dodo-12-37/TrackSense/Composants/Acceleromètre/QMC5883L - Boussole/HMC5883L(Or QMC5883L) Electronic.pdf

# HMC5883L(Or QMC5883L) Electronic Compass

In ourProfessional Kit, there exist two kinds of Compass module. One kind uses HMC5883L module, the other uses QMC5883L module. You will get one of them when you get the Professional Kit. They don't have too much difference. HMC5883Lis made by Honeywell. but because the production is about to be stopped, so we use a similar compass module-QMC5883Linstead. QMC5883Lis made by a Chinese company, they get the production authorization of HMC5883L from Honeywell, and rename it QMC5883L. So QMC5883Land HMC5883Lbasically are the same, they shares the same hardware design. Just their register is a bit different. We only need to change the software a bit.

When you got the Professional Kit, please check which compass module you get based on the following picture. The HMC5883Lhas a label "L883"on it, while QMC5883Lcomes with "5883"

HMC5883LElectronic Compass | QMC5883LElectronic Compass
HMC5883LElectronic Compass | QMC5883LElectronic Compass

# HMC5883L Electronic Compass

## Introduction

3-Axis Compass module, I2C based Honeywell HMC5883 digital compass. This ASIC is equipped with high resolution HMC118X magneto-resistive sensors and a 12-bitADC. It provides compass heading accuracy up to 1° to 2°. Signal conditioning like amplification, automatic degaussing strap drivers and offset cancellation are inbuilt. This module also includes a MIC5205-2.5 voltage regulator for power supply requirement. Hence user can connect any 3.3V to 6V DC power supply.

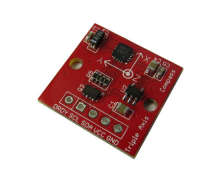
[picture p6: figure]

## Features

- I2C interface
- Compatible with 3.3V-5.0V voltage level
- Max 116Hz output rate
- High heading accuracy

## Usage

Below is a registermap that might help you understand what you can get from this module. There are totally 13 registers provided by HMC5883L. Out of three registers - Configuration registerA, Configuration RegisterB and Mode Register decide the working mode of the device. The remaining registers are read only data output registers, status register and identification registers.

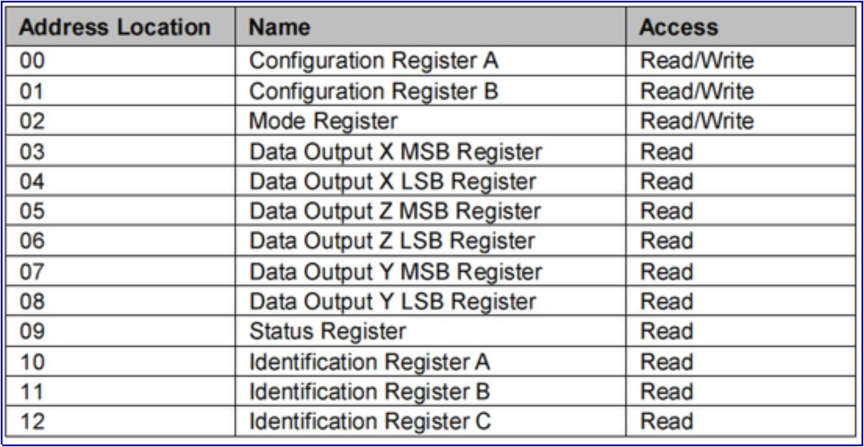
[picture p7: figure]

This demo is going to show you how to read raw data, how to calibrate the data with your local magnetic declination angle and how to get heading angle.
First off, before any action you are going to take, you need to prepare a parameter you are going to use in your demo. That's your local magnetic declination.
You can find it out in degree via the magnetic declination webpage. For example, mine is -2°37’, which is -2.617 degree.
Then transfer it from degree to radians, and there you get the "declinationAngle". For example, in my case, declinationAngle = -2.617 / （2*π）= -0.0456752665 rad. Three significant figures are enough. So I would shorten it into -0.0456 rad. And this is the parameter you are going to replace the value of "declinationAngle"in the domo code with.
Now let's start to run your compass.
1. Connect the HMC5883LElectronic Compass to Arduino via the I2C port.
2. Download the library file: HMC5883L Compass library. Unzip it into the libraries file of Arduino IDE by the path: ..\arduino-1.0.1\libraries.
3. Open the demo by the path:File -> Example ->Digital Compass ->HMC5883L_Example.
4. Replace the value of variable "declinitionAngle"with the one you've figured out already.
5. Upload the Code.
6. Check the output result by opening the serial monitor.

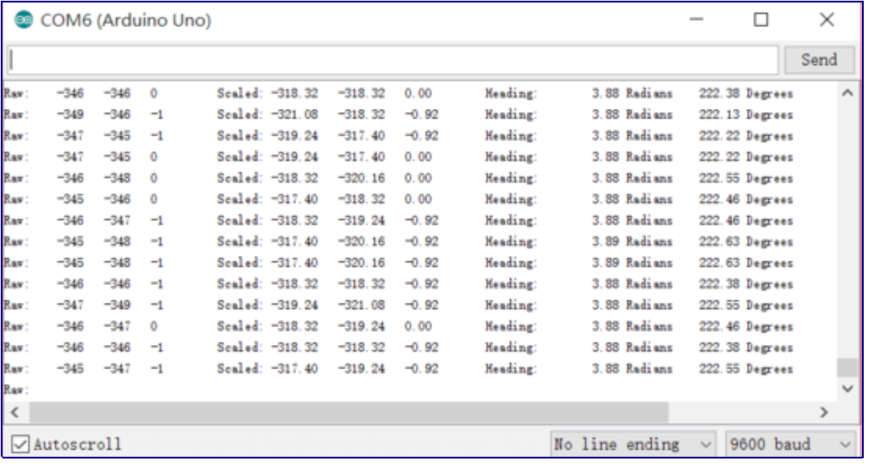
[picture p8: figure]

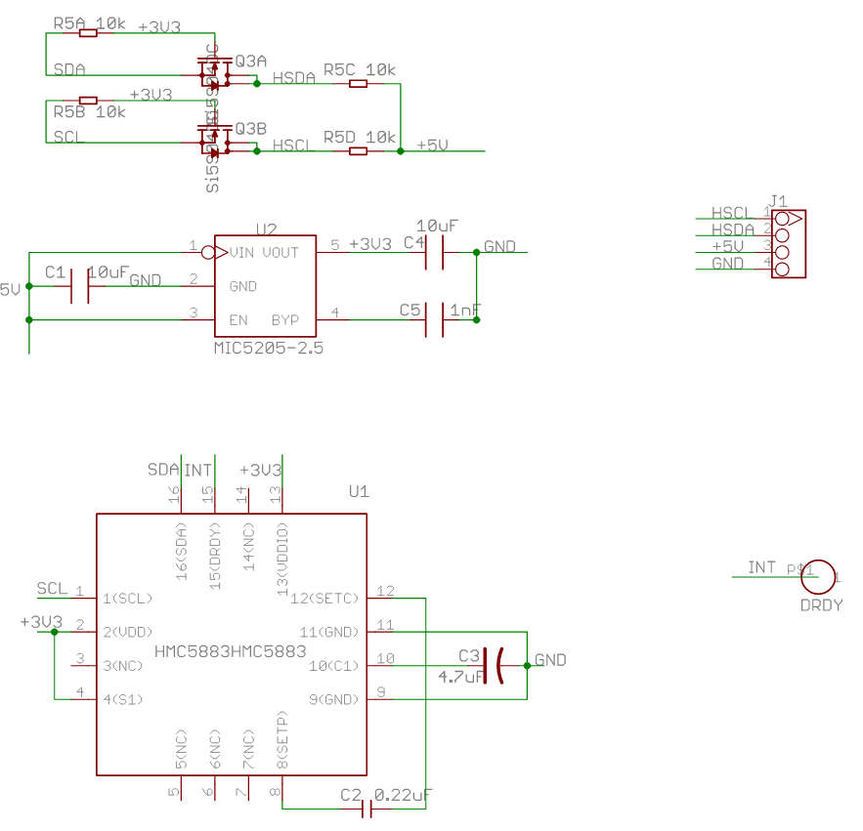
[picture p9: figure]

# QMC5883L Electronic Compass

## Introduction

3-Axis Compass module, I2C based QMC5883 digital compass. This ASIC is equipped with high resolution magneto-resistive sensors and a 16-bit ADC. It provides compass heading accuracy up to 1° to 2°. Signal conditioning like amplification, automatic degaussing strap drivers and offset cancellation are inbuilt. This module also includes a MIC5205-2.5 voltage regulator forpower supply requirement. Hence user can connect any 3.3V to 6V DC power supply.

Features

- I2C interface
- Compatible with 3.3V-5.0V voltage level
- Max 200Hz output rate
- High heading accuracy

## Usage

Below is a registermap that might help you understand what you can get from this module. There are totally 14 registers provided by QMC5883L. Two Control Registers decide the working mode of the device, they come with address "09H"and "0AH". Most of the remaining registers are read only data output registers, status register and identification registers.

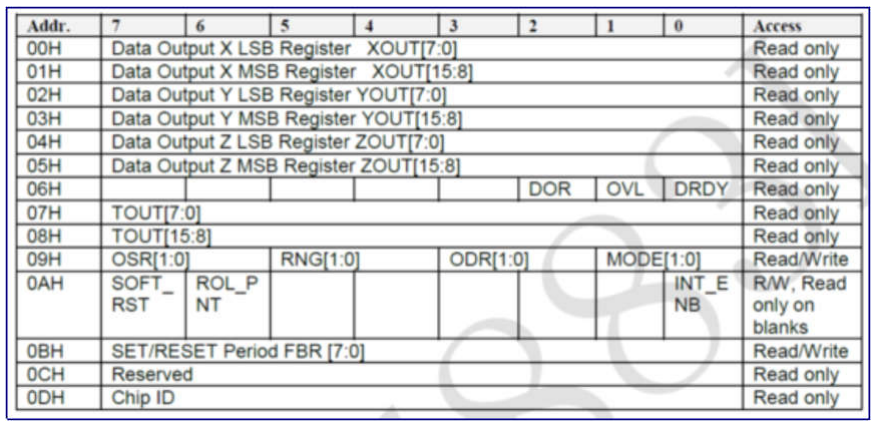
[picture p10: figure]

In this example we will make the module output the heading angle between South and this module.

### 1. Connect the QMC5883LElectronic Compass to Arduino via the I2C port. Make sure the

QMC5883L module is horizontal。
2. Download the library file: QMC5883L Compass library. Unzip it into the libraries file of Arduino IDE by the path: ..\arduino-1.0.1\libraries.
3. Open the demo by the path:File -> Example ->Digital Compass ->QMC5883L_Example.
4. Upload the Code.
5. Check the output result by opening the serial monitor.

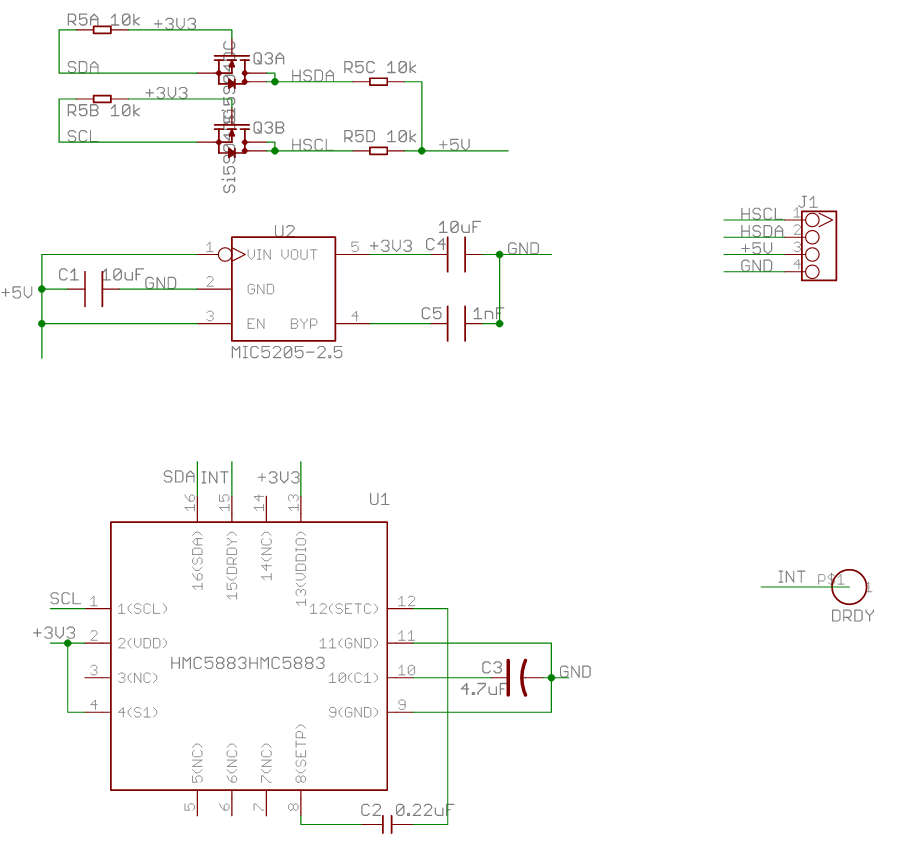
[picture p11: figure]
