dodo-12-37/TrackSense/Composants/Acceleromètre/Dessous Sensor.jpg

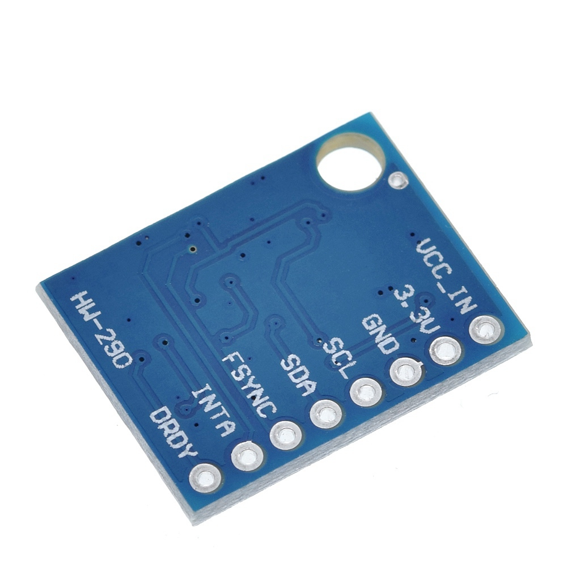
Composants/Acceleromètre/Dessous Sensor.jpg
