dodo-12-37/TrackSense/Composants/Acceleromètre/Dessus Dessous Sensor.jpg

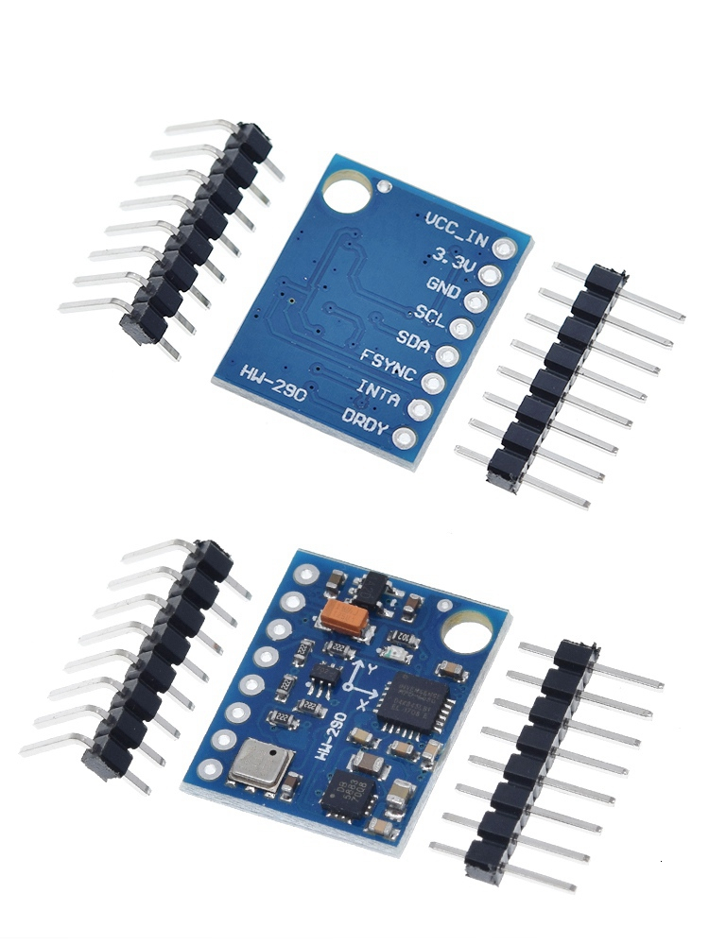
Composants/Acceleromètre/Dessus Dessous Sensor.jpg
