dodo-12-37/TrackSense/Composants/Acceleromètre/Dessus Sensor 2.jpg

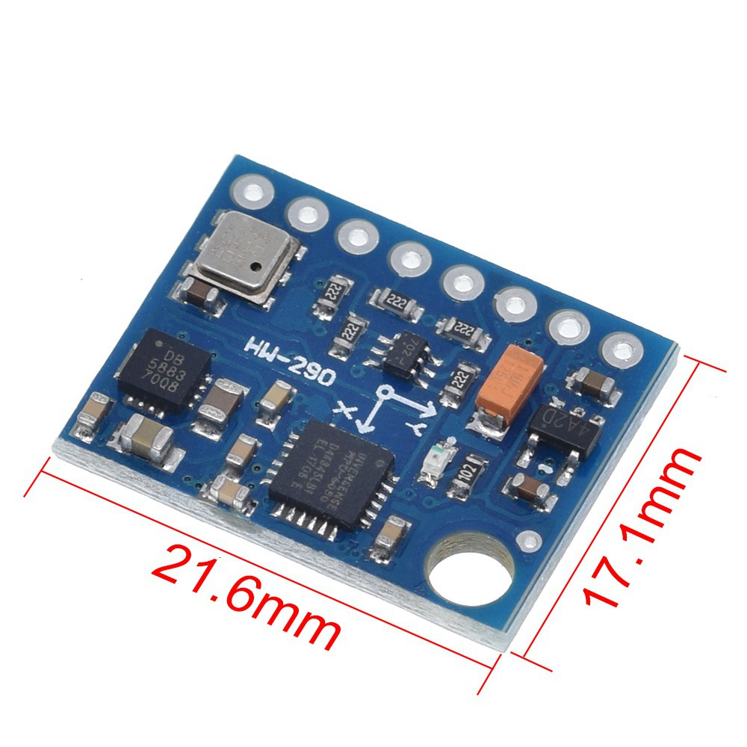
Composants/Acceleromètre/Dessus Sensor 2.jpg
