dodo-12-37/TrackSense/Composants/Acceleromètre/Dessus Sensor.jpg

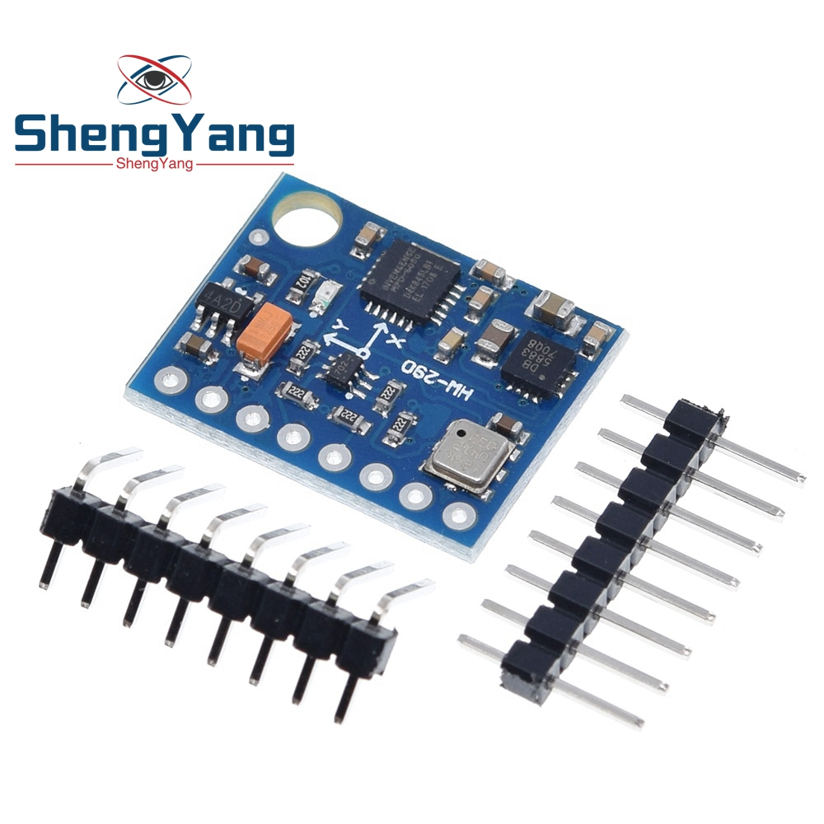
Composants/Acceleromètre/Dessus Sensor.jpg
