dodo-12-37/TrackSense/Composants/Acceleromètre/GY-87-Module-wire-4.jpg

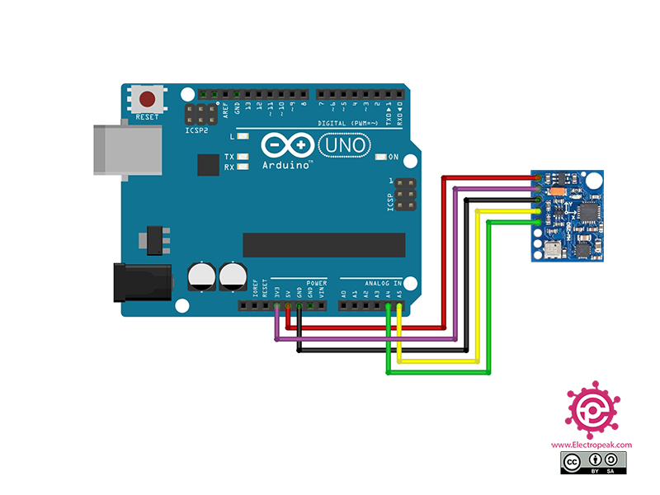
Composants/Acceleromètre/GY-87-Module-wire-4.jpg
