dodo-12-37/TrackSense/Composants/Acceleromètre/GY-87-Pin-2.jpg

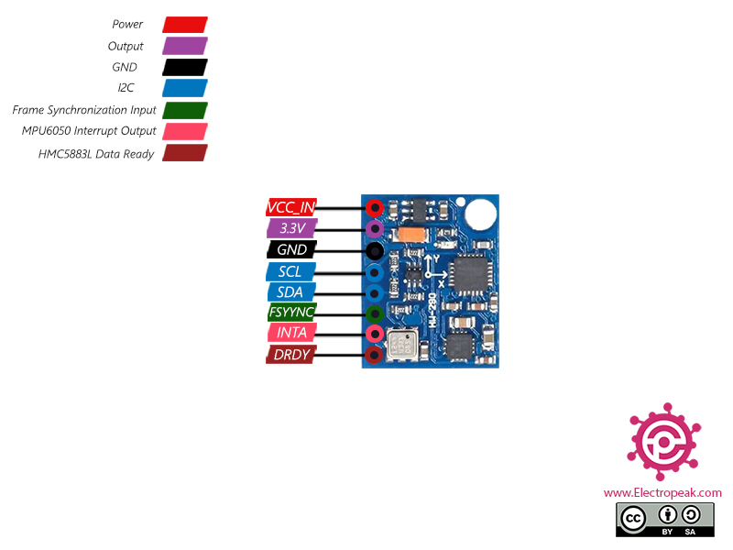
Composants/Acceleromètre/GY-87-Pin-2.jpg
