dodo-12-37/TrackSense/Composants/Acceleromètre/QMC5883L - Boussole/Dessins Boussole/Boussoles2.png

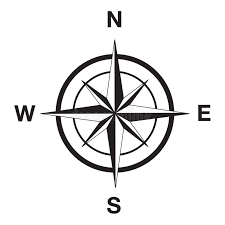
Composants/Acceleromètre/QMC5883L - Boussole/Dessins Boussole/Boussoles2.png
