dodo-12-37/TrackSense/Composants/Boitier/Photos_boitier/Bitoniau 1.png

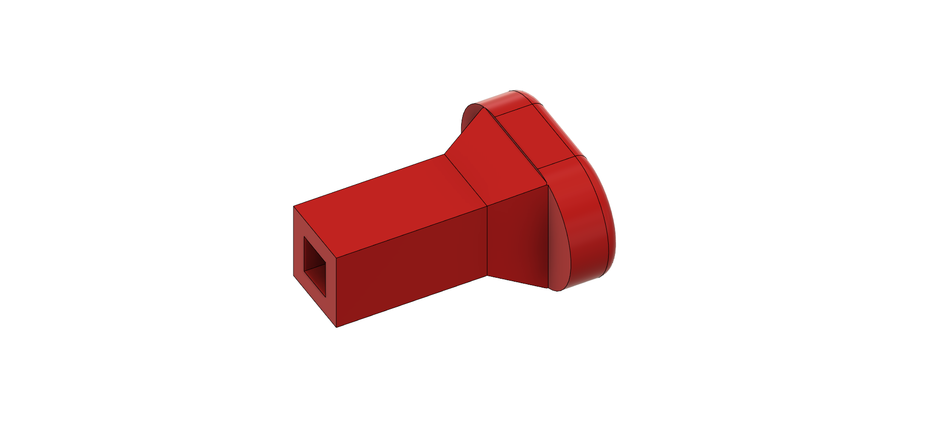
Composants/Boitier/Photos_boitier/Bitoniau 1.png
