dodo-12-37/TrackSense/Composants/Boitier/Photos_boitier/Bitoniau 2.png

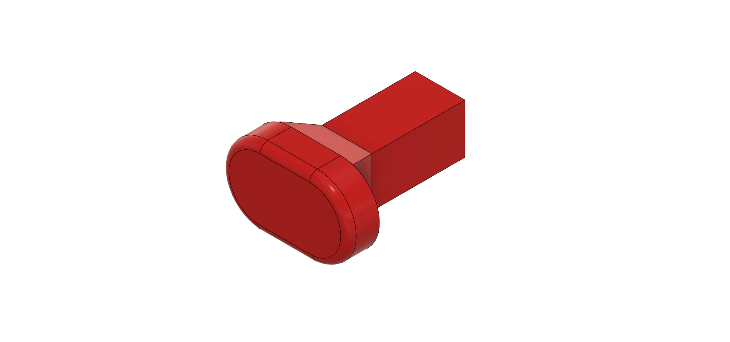
Composants/Boitier/Photos_boitier/Bitoniau 2.png
