dodo-12-37/TrackSense/Composants/Boitier/Photos_boitier/Boitier 0.jpg

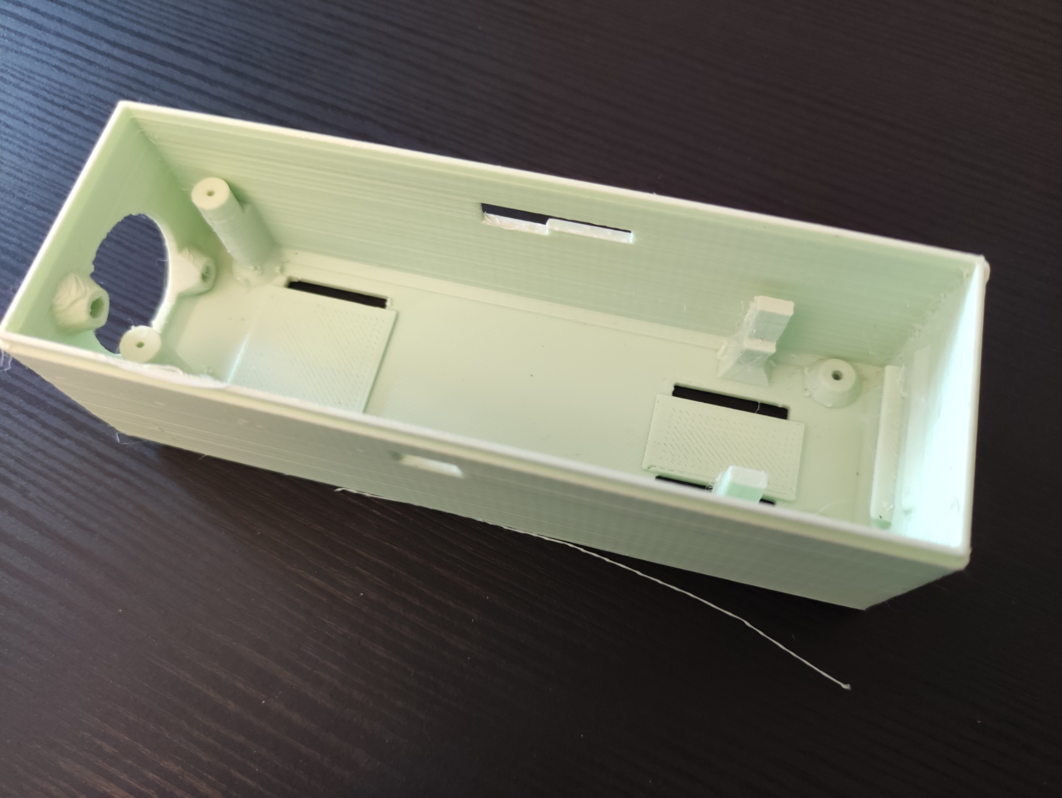
Composants/Boitier/Photos_boitier/Boitier 0.jpg
