dodo-12-37/TrackSense/Composants/Boitier/Photos_boitier/Boitier 3.png

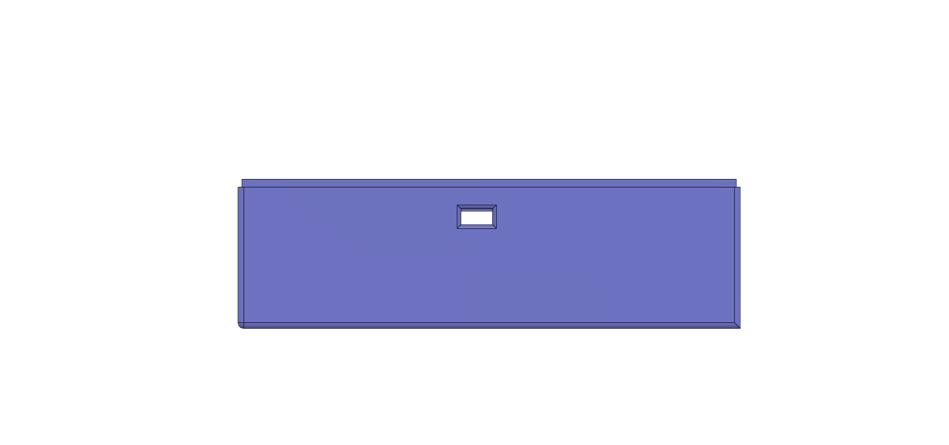
Composants/Boitier/Photos_boitier/Boitier 3.png
