dodo-12-37/TrackSense/Composants/Boitier/Photos_boitier/Boitier 5.png

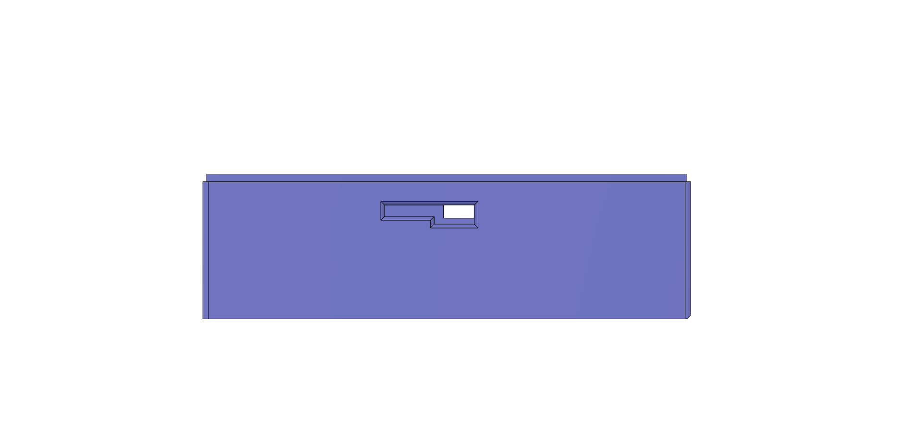
Composants/Boitier/Photos_boitier/Boitier 5.png
