dodo-12-37/TrackSense/Composants/Boitier/Photos_boitier/Couvercle 1.png

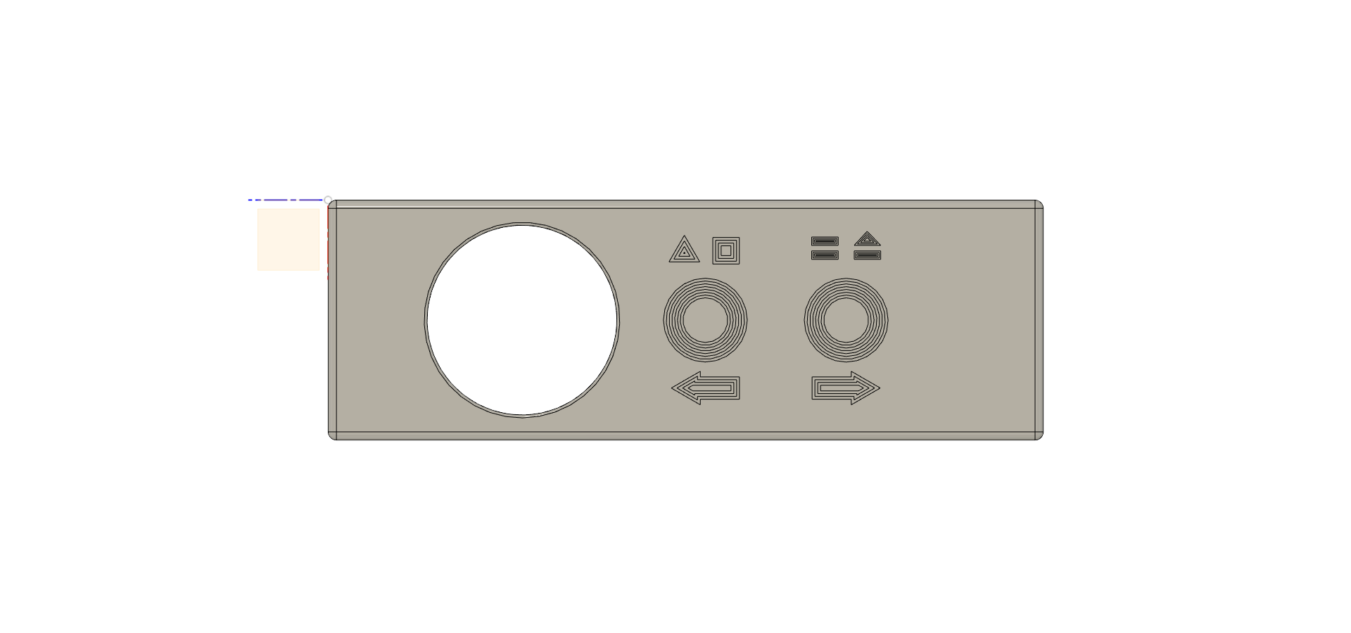
Composants/Boitier/Photos_boitier/Couvercle 1.png
