dodo-12-37/TrackSense/Composants/Boitier/Photos_boitier/Ensemble 1.jpg

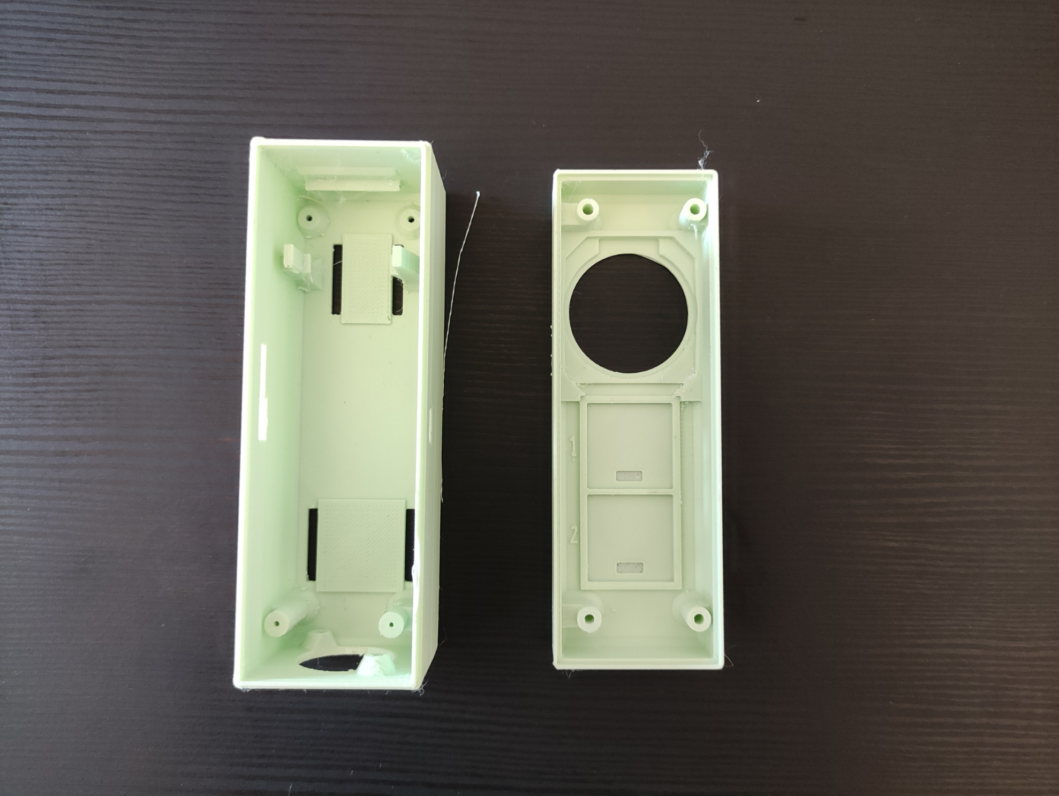
Composants/Boitier/Photos_boitier/Ensemble 1.jpg
