dodo-12-37/TrackSense/Composants/Boitier/Photos_boitier/Ensemble 2.png

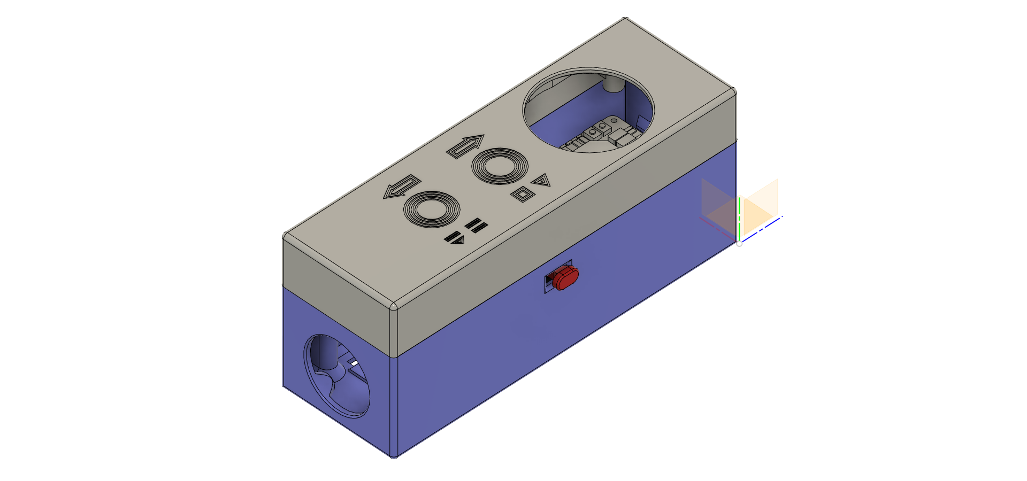
Composants/Boitier/Photos_boitier/Ensemble 2.png
