dodo-12-37/TrackSense/Composants/Boutons tactiles/Dessous Sensor.jpg

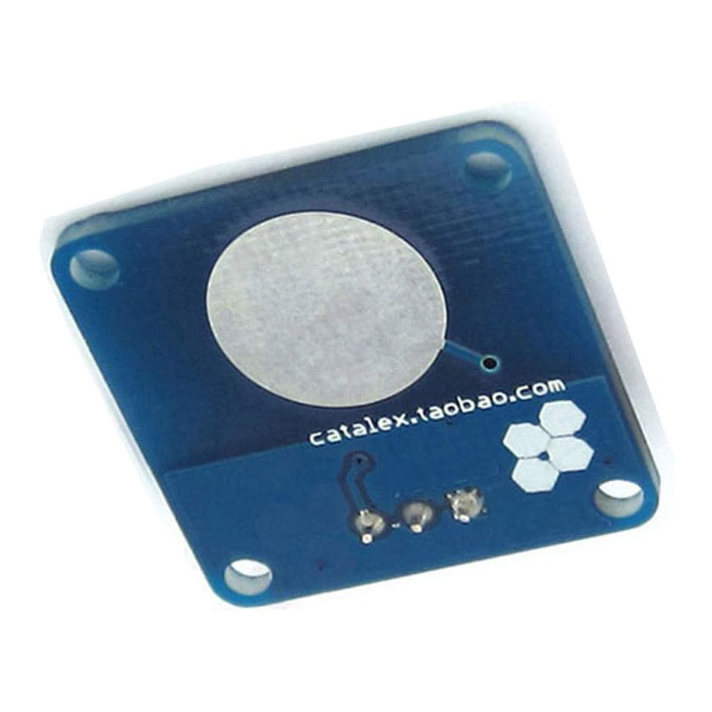
Composants/Boutons tactiles/Dessous Sensor.jpg
