dodo-12-37/TrackSense/Composants/Boutons tactiles/Dessus Sensor.jpg

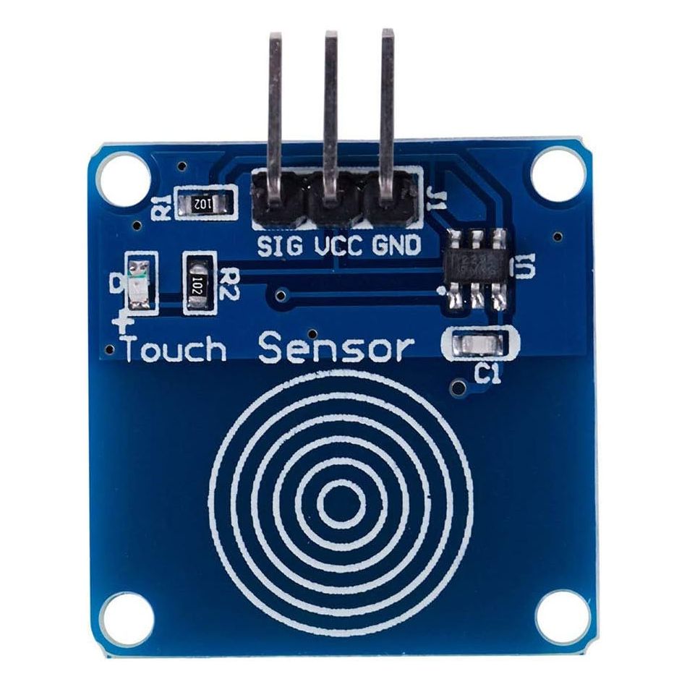
Composants/Boutons tactiles/Dessus Sensor.jpg
