dodo-12-37/TrackSense/Composants/Boutons tactiles/Digital-Sensor-TTP223B-Module-Capacitive2.webp

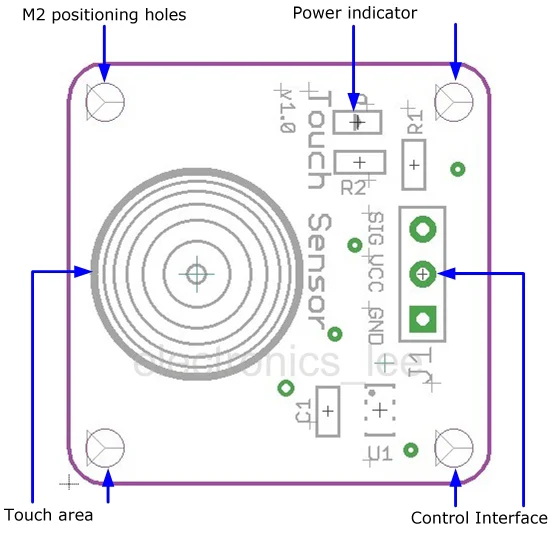
Composants/Boutons tactiles/Digital-Sensor-TTP223B-Module-Capacitive2.webp
