dodo-12-37/TrackSense/Composants/Boutons tactiles/Dimensions 2.JPG

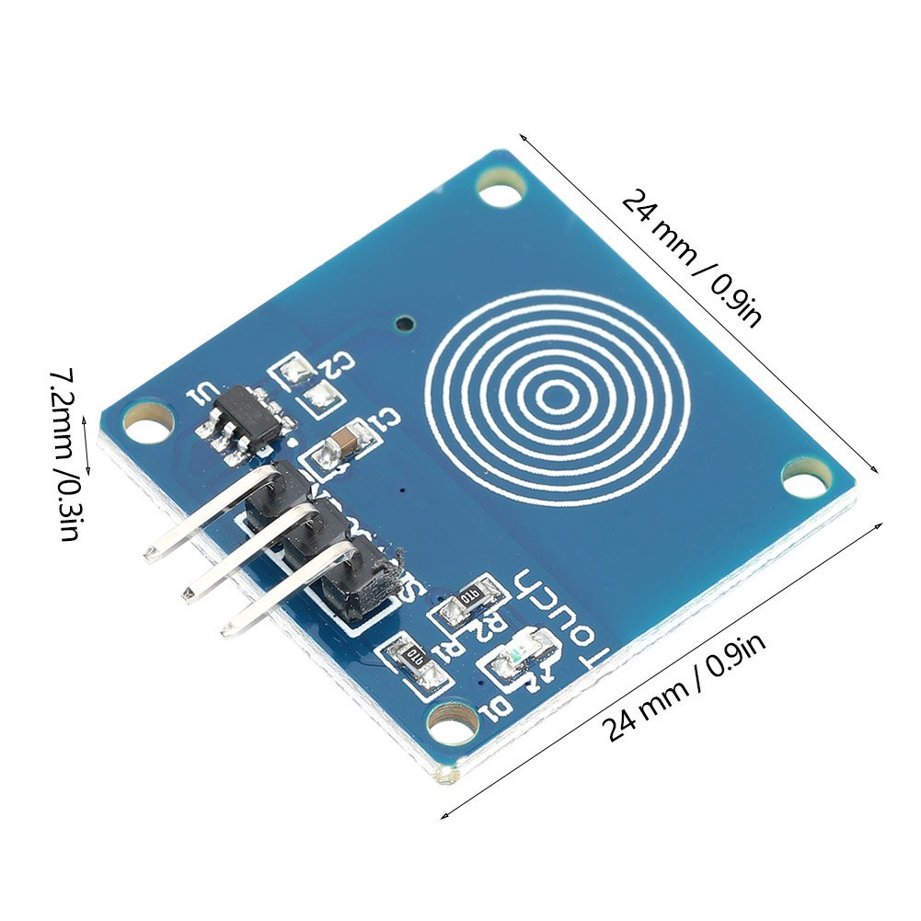
Composants/Boutons tactiles/Dimensions 2.JPG
