dodo-12-37/TrackSense/Composants/Boutons tactiles/Dimensions.JPG

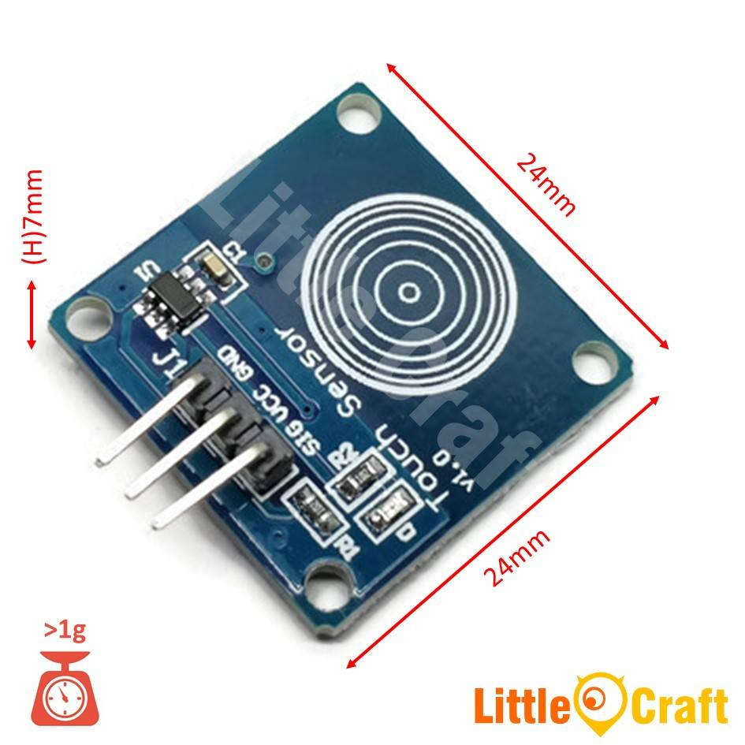
Composants/Boutons tactiles/Dimensions.JPG
