dodo-12-37/TrackSense/Composants/Boutons tactiles/Exemple Connexion Arduino 2.jpg

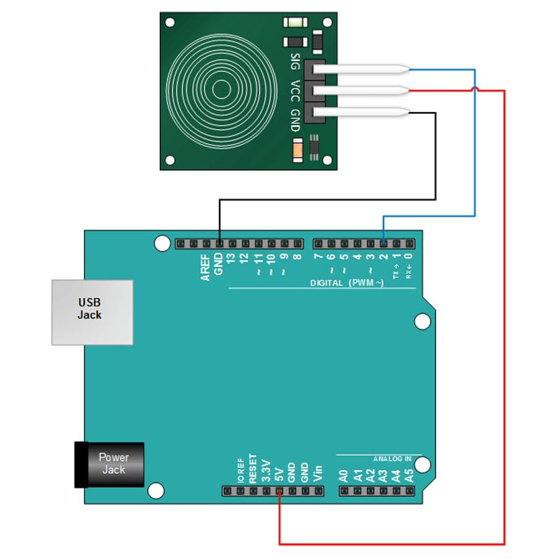
Composants/Boutons tactiles/Exemple Connexion Arduino 2.jpg
