dodo-12-37/TrackSense/Composants/Boutons tactiles/Exemple Connexion Arduino.jpg

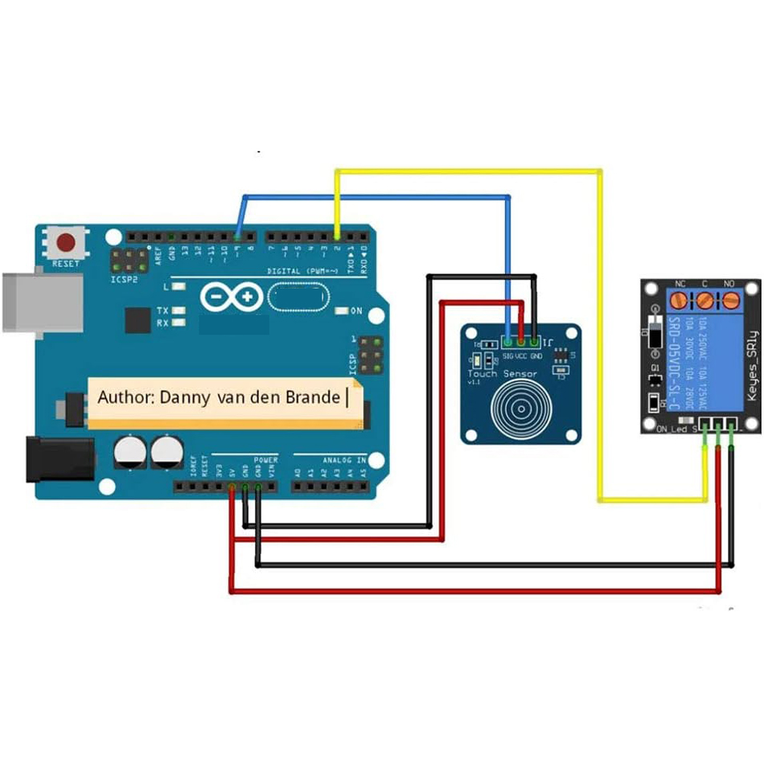
Composants/Boutons tactiles/Exemple Connexion Arduino.jpg
