dodo-12-37/TrackSense/Composants/Boutons tactiles/Exemple Connexion.jpg

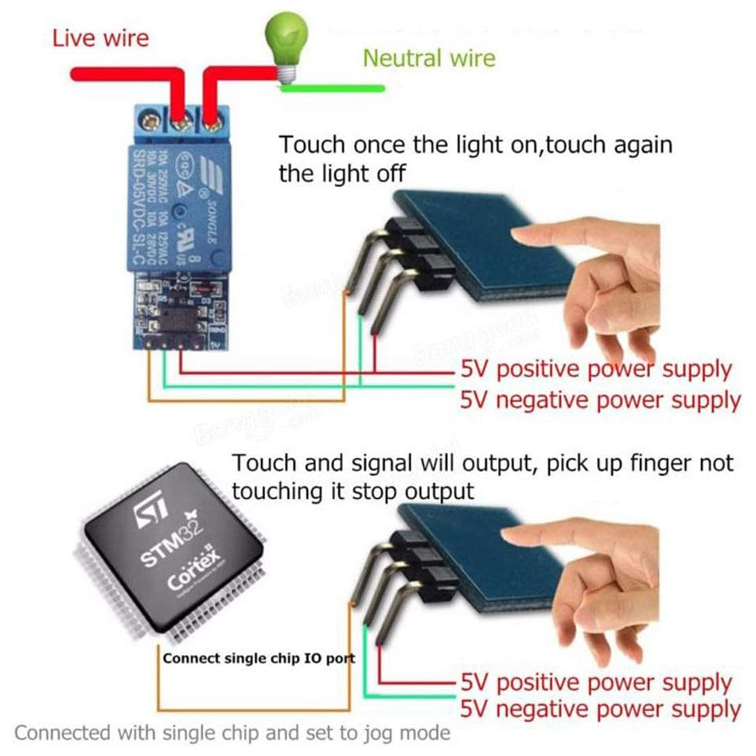
Composants/Boutons tactiles/Exemple Connexion.jpg
