dodo-12-37/TrackSense/Composants/Buzzer/Dessus & Dessous Sensor 2.jpg

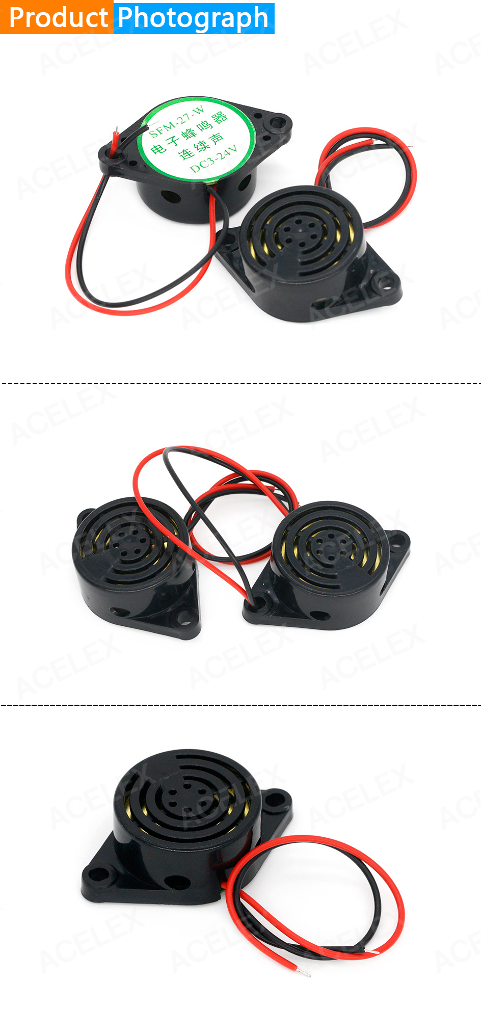
Composants/Buzzer/Dessus & Dessous Sensor 2.jpg
