dodo-12-37/TrackSense/Composants/Buzzer/Dessus & Dessous Sensor.jpg

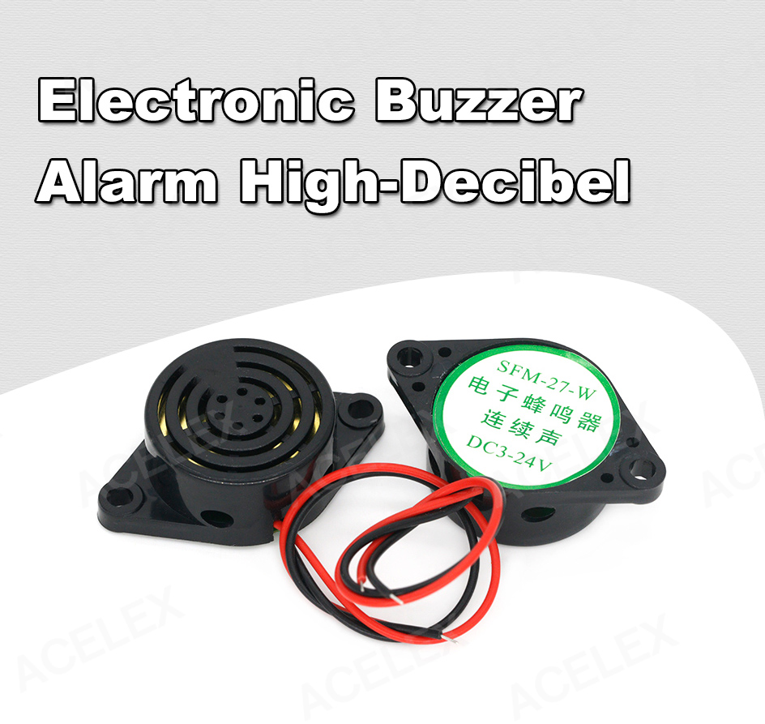
Composants/Buzzer/Dessus & Dessous Sensor.jpg
