dodo-12-37/TrackSense/Composants/Buzzer/Dimension_SFM-20B.jpg

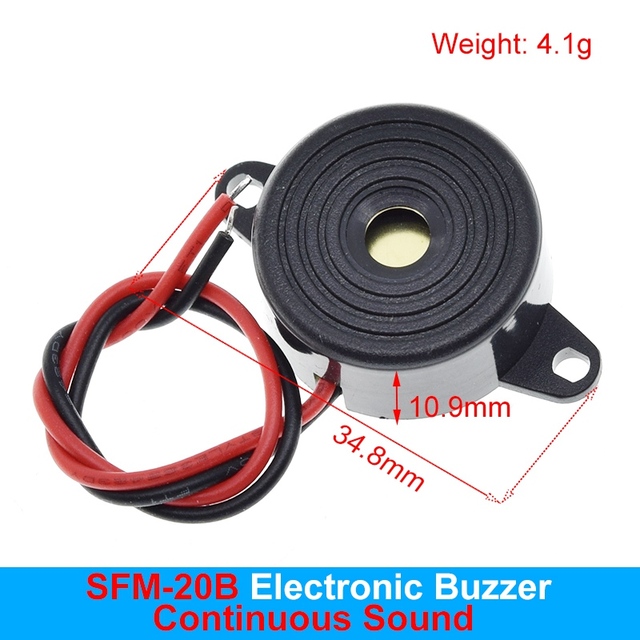
Composants/Buzzer/Dimension_SFM-20B.jpg
