dodo-12-37/TrackSense/Composants/Buzzer/Dimensions_Schéma_SFM-20B.jpg

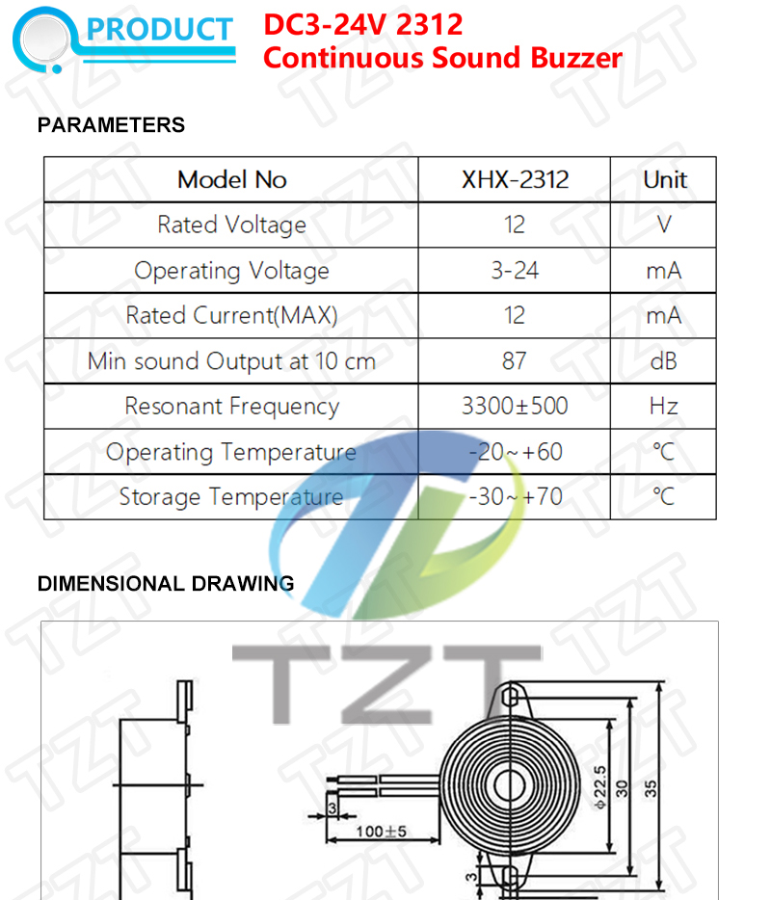
Composants/Buzzer/Dimensions_Schéma_SFM-20B.jpg
