dodo-12-37/TrackSense/Composants/Buzzer/Dimensions_SchémaComplet_SFM-20B.jpg

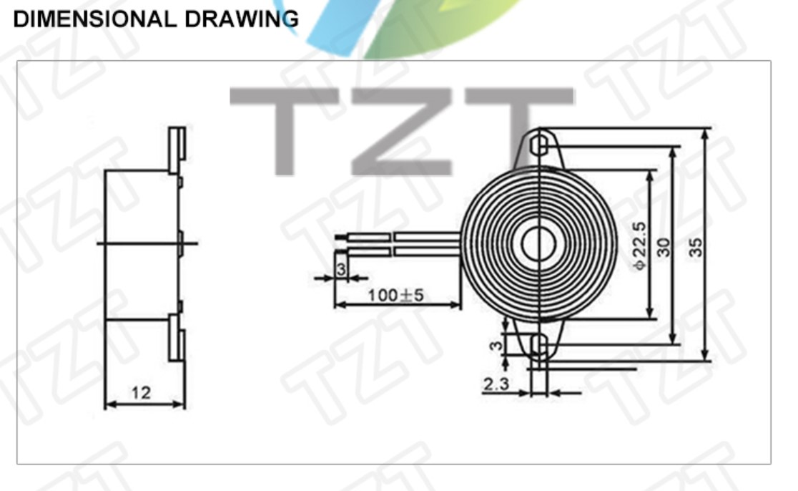
Composants/Buzzer/Dimensions_SchémaComplet_SFM-20B.jpg
