dodo-12-37/TrackSense/Composants/Buzzer/SFM-27/Dimensions_SFM-27_ContinuousSound.jpg

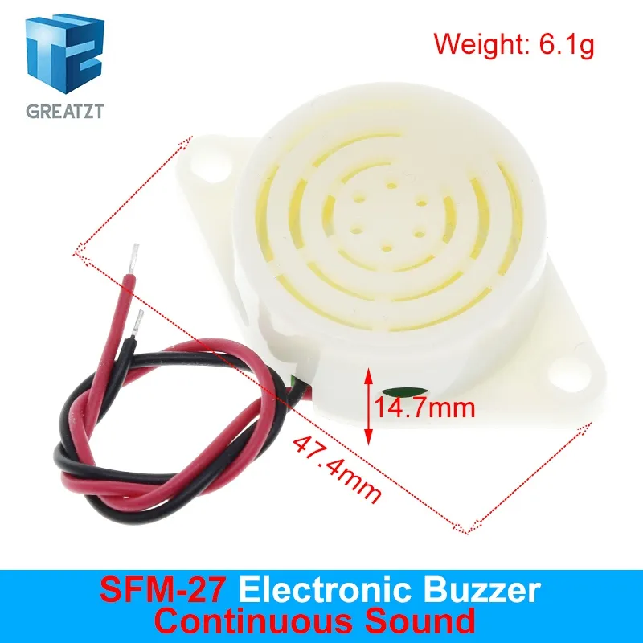
Composants/Buzzer/SFM-27/Dimensions_SFM-27_ContinuousSound.jpg
