dodo-12-37/TrackSense/Composants/Buzzer/SFM-27/Paramètres du Produit SFM-27.jpg

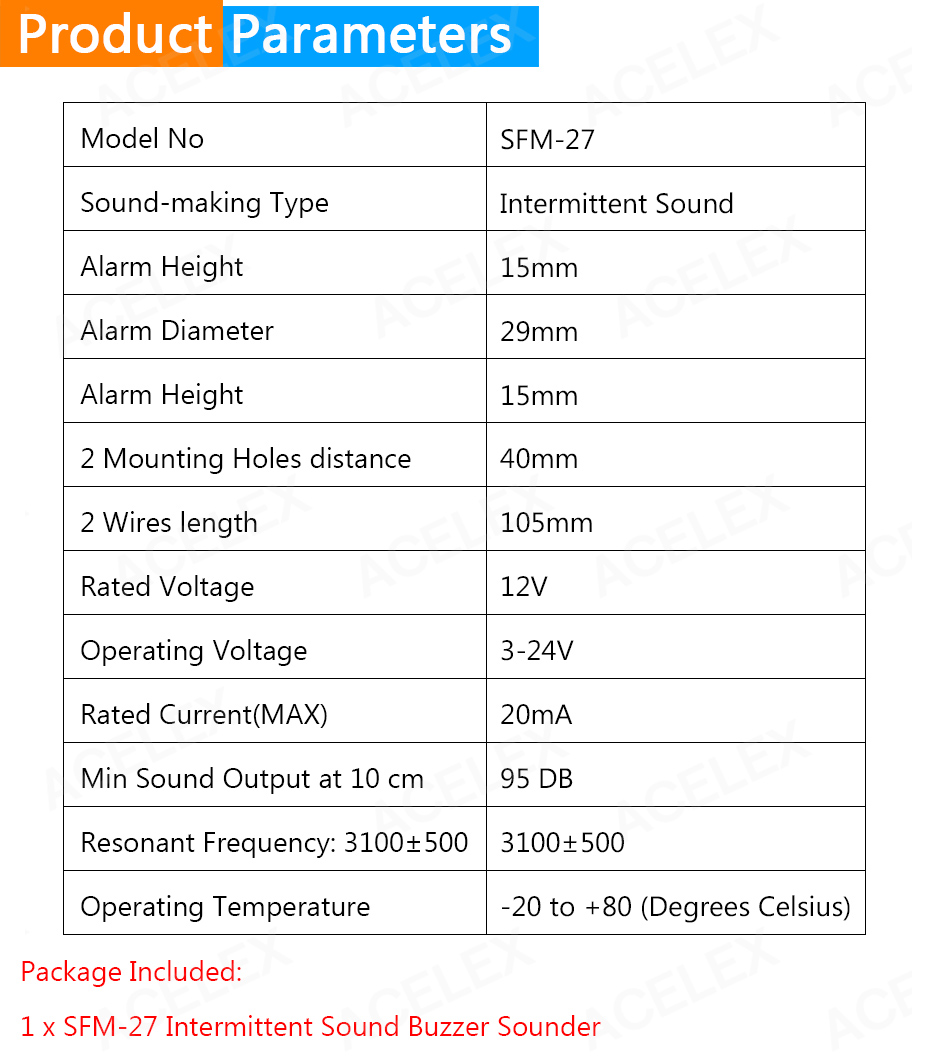
Composants/Buzzer/SFM-27/Paramètres du Produit SFM-27.jpg
