dodo-12-37/TrackSense/Composants/Buzzer/Speaker Alarme SFM-20B XHX-2312 (Pt pas celui acheté).jpg

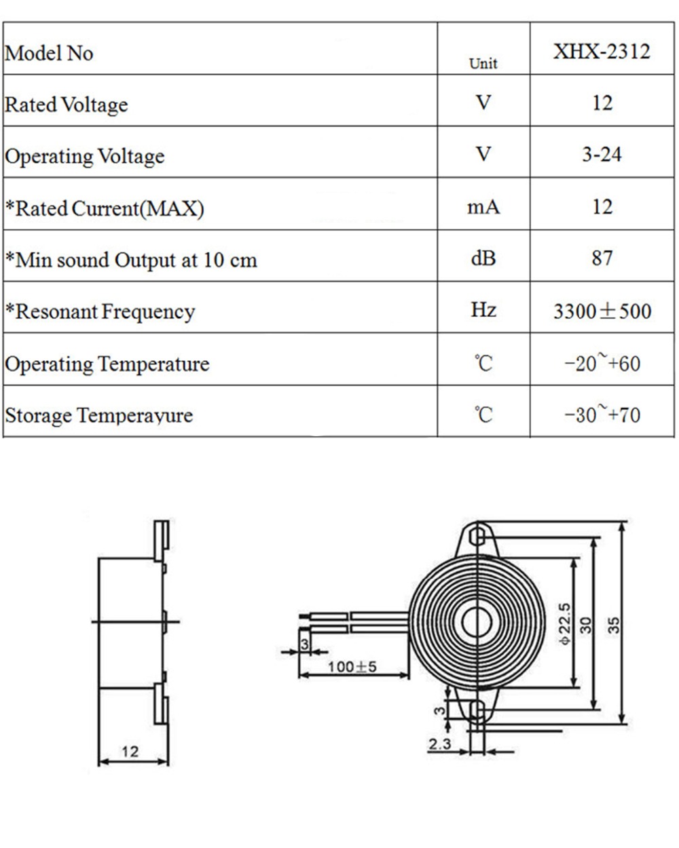
Composants/Buzzer/Speaker Alarme SFM-20B XHX-2312 (Pt pas celui acheté).jpg
