dodo-12-37/TrackSense/Composants/Lilygo/Circuit électrique partielle LILYGO.png

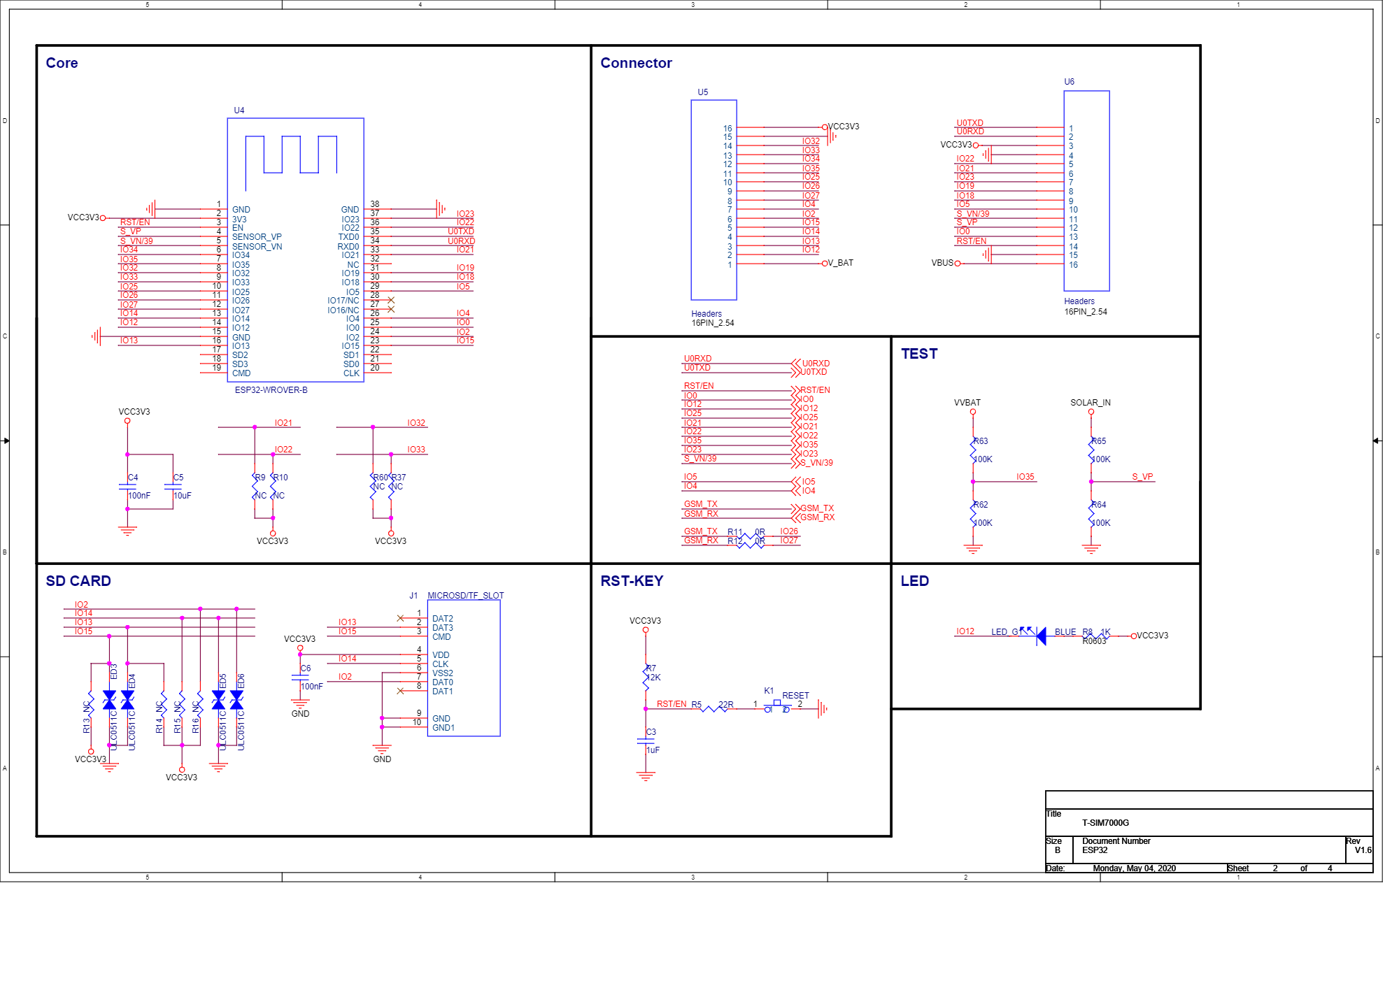
Composants/Lilygo/Circuit électrique partielle LILYGO.png
