dodo-12-37/TrackSense/Composants/Lilygo/Description Aliexpress.png

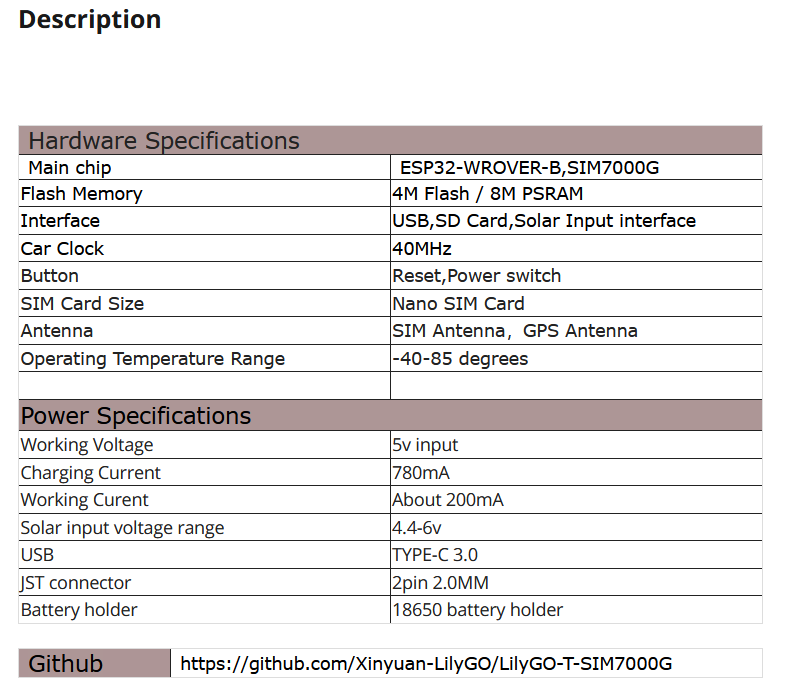
Composants/Lilygo/Description Aliexpress.png
