dodo-12-37/TrackSense/Composants/Lilygo/Dimension de la Plaquette V1.0.png

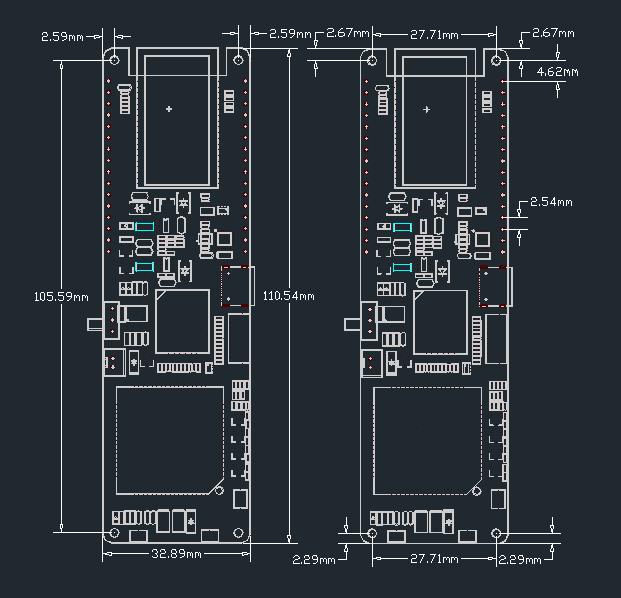
Composants/Lilygo/Dimension de la Plaquette V1.0.png
