dodo-12-37/TrackSense/Composants/Lilygo/Dimension de la Plaquette V1.1.png

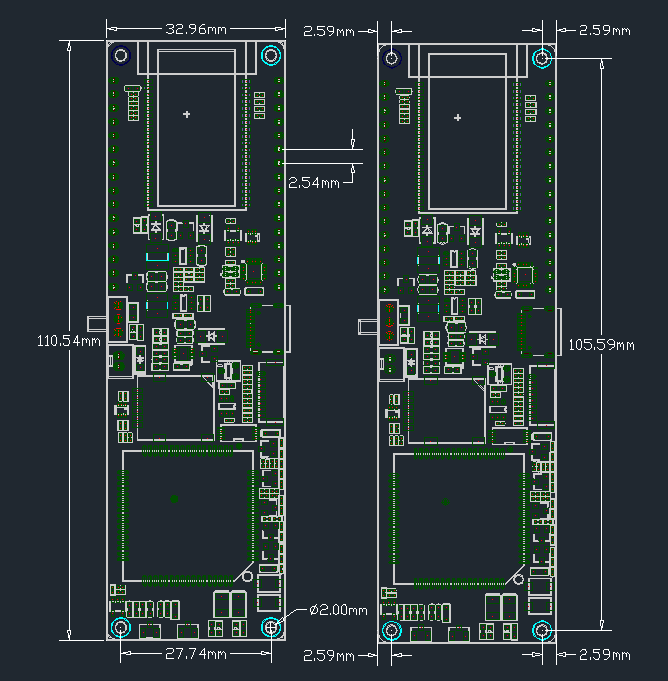
Composants/Lilygo/Dimension de la Plaquette V1.1.png
