dodo-12-37/TrackSense/Composants/Lilygo/Emplacement des Antennes.jpg

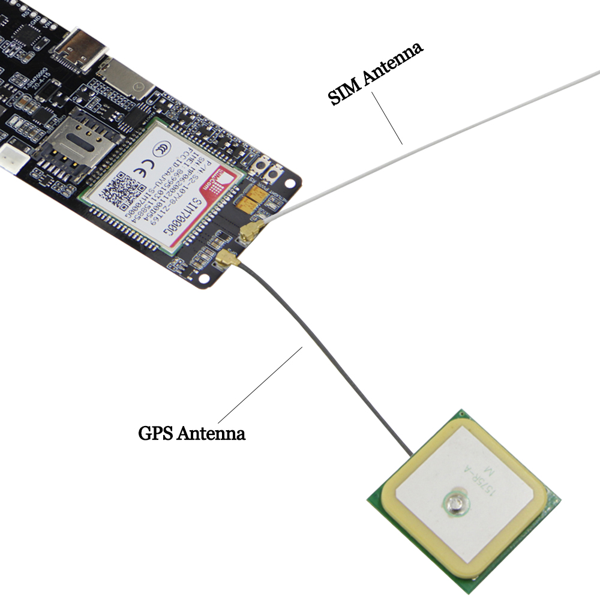
Composants/Lilygo/Emplacement des Antennes.jpg
