dodo-12-37/TrackSense/Composants/Lilygo/Emplacement des composantes 2 - V1.1.jpg

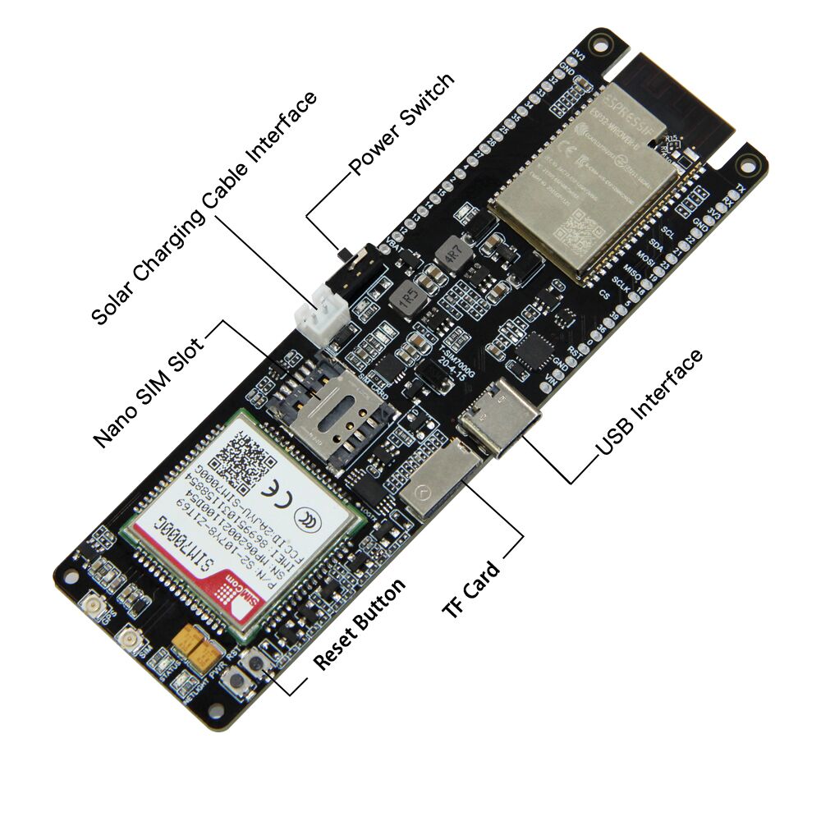
Composants/Lilygo/Emplacement des composantes 2 - V1.1.jpg
