dodo-12-37/TrackSense/Composants/Lilygo/GPS/AT command in the serial terminal.png

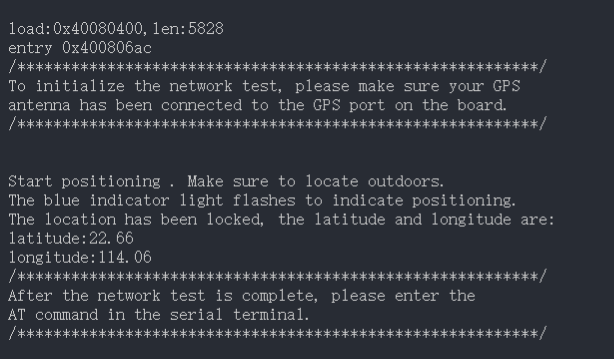
Composants/Lilygo/GPS/AT command in the serial terminal.png
