dodo-12-37/TrackSense/Composants/Lilygo/LILYGO-SIM7000G-ESP32-Différence entre les versions.jpg

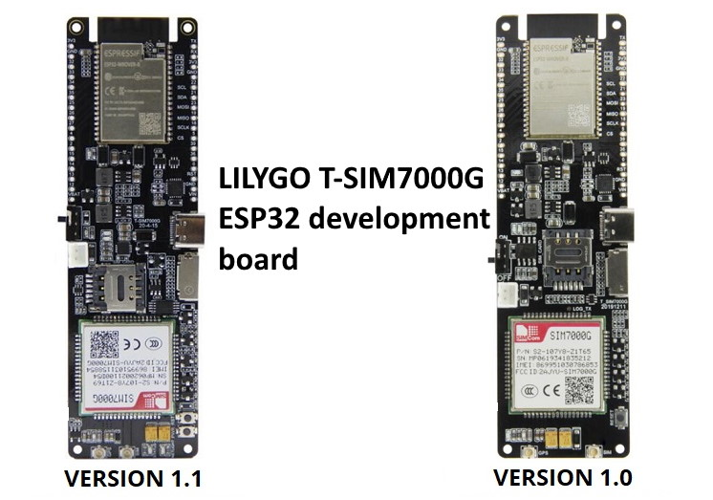
Composants/Lilygo/LILYGO-SIM7000G-ESP32-Différence entre les versions.jpg
