dodo-12-37/TrackSense/Composants/Lilygo/LILYGO-SIM7000G-ESP32-V1_0_pinout.jpg

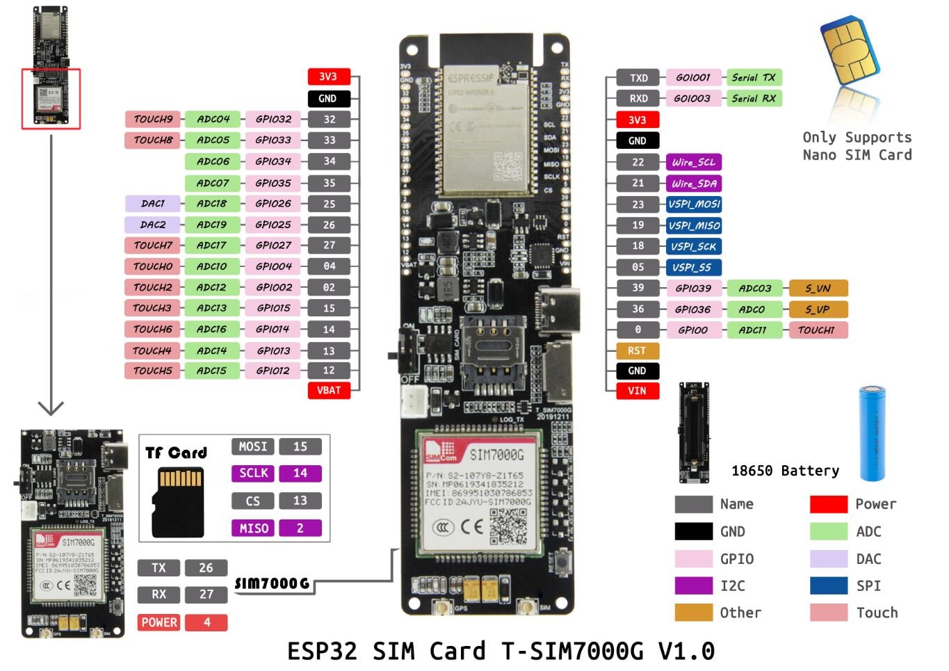
Composants/Lilygo/LILYGO-SIM7000G-ESP32-V1_0_pinout.jpg
