dodo-12-37/TrackSense/Composants/Lilygo/Modification de la Nouvelle Version 1.1.png

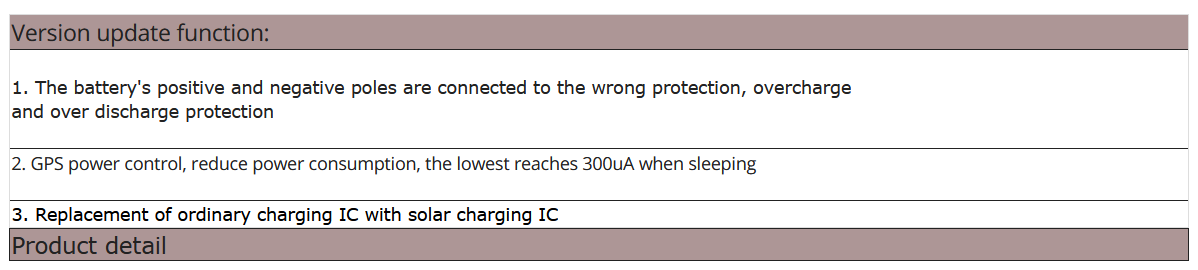
Composants/Lilygo/Modification de la Nouvelle Version 1.1.png
