dodo-12-37/TrackSense/Composants/Lilygo/Shipping List.jpg

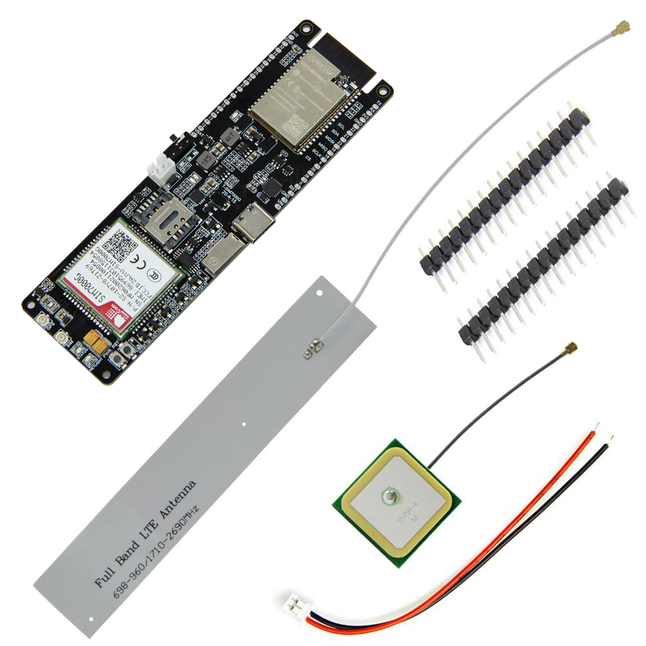
Composants/Lilygo/Shipping List.jpg
