dodo-12-37/TrackSense/Composants/PCB/Choix couleurs PCB.jpg

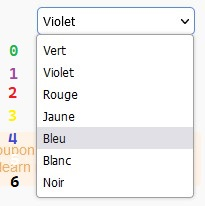
Composants/PCB/Choix couleurs PCB.jpg
