dodo-12-37/TrackSense/Composants/PCB/Inspiration externe/Capture d’écran 2023-07-04 142751.png

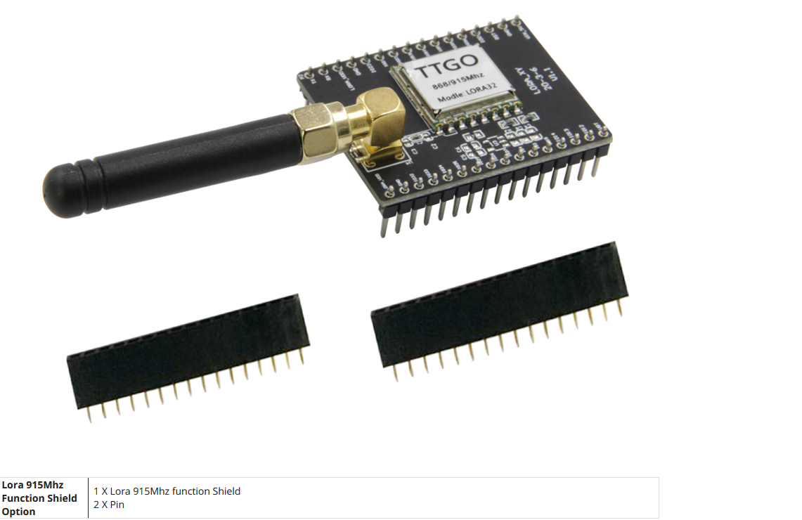
Composants/PCB/Inspiration externe/Capture d’écran 2023-07-04 142751.png
