dodo-12-37/TrackSense/Composants/PCB/V1.0/Dessus 3D TrackSense V1.0.jpg

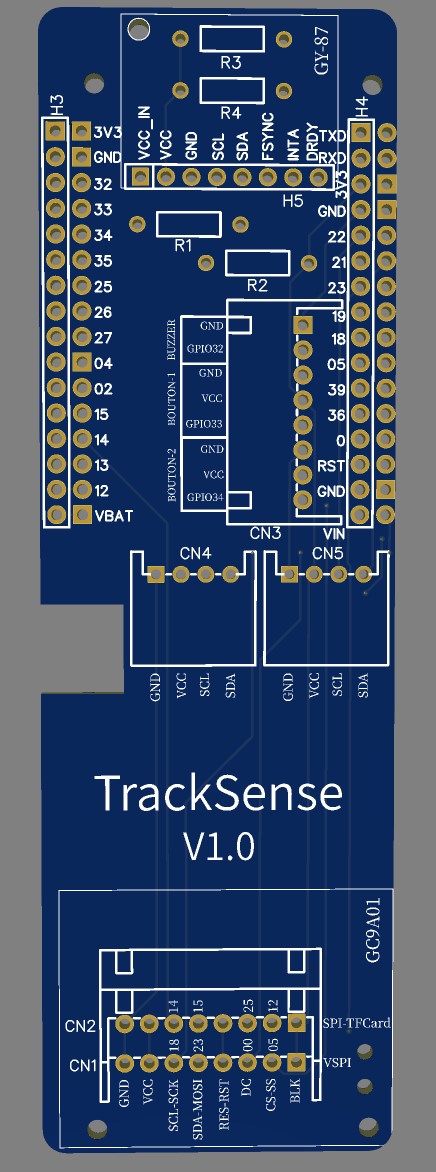
Composants/PCB/V1.0/Dessus 3D TrackSense V1.0.jpg
