dodo-12-37/TrackSense/Composants/PCB/V1.0/Paramètres_Commande_PCB_sur_JLCPCB.png

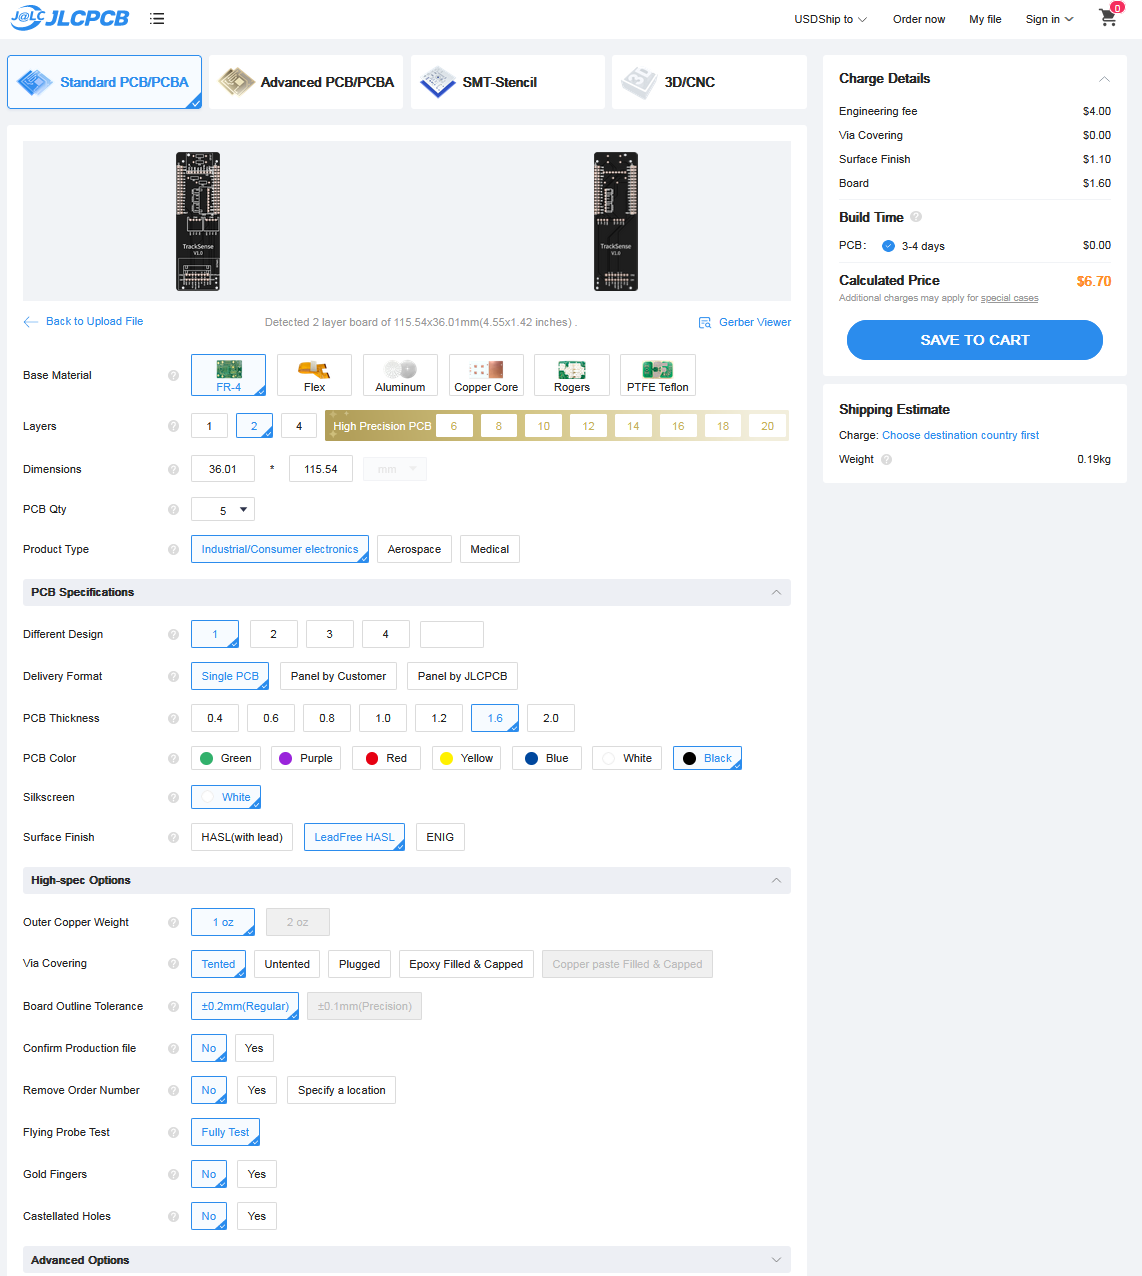
Composants/PCB/V1.0/Paramètres_Commande_PCB_sur_JLCPCB.png
