dodo-12-37/TrackSense/Composants/PCB/V1.0/PCB_PCB_TrackSense_Big_115.54X36mm_V1.0_2023-07-17.png

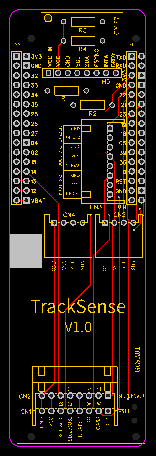
Composants/PCB/V1.0/PCB_PCB_TrackSense_Big_115.54X36mm_V1.0_2023-07-17.png
