dodo-12-37/TrackSense/Composants/PCB/V1.0/Schematic_TrackSense_2023-07-17.png

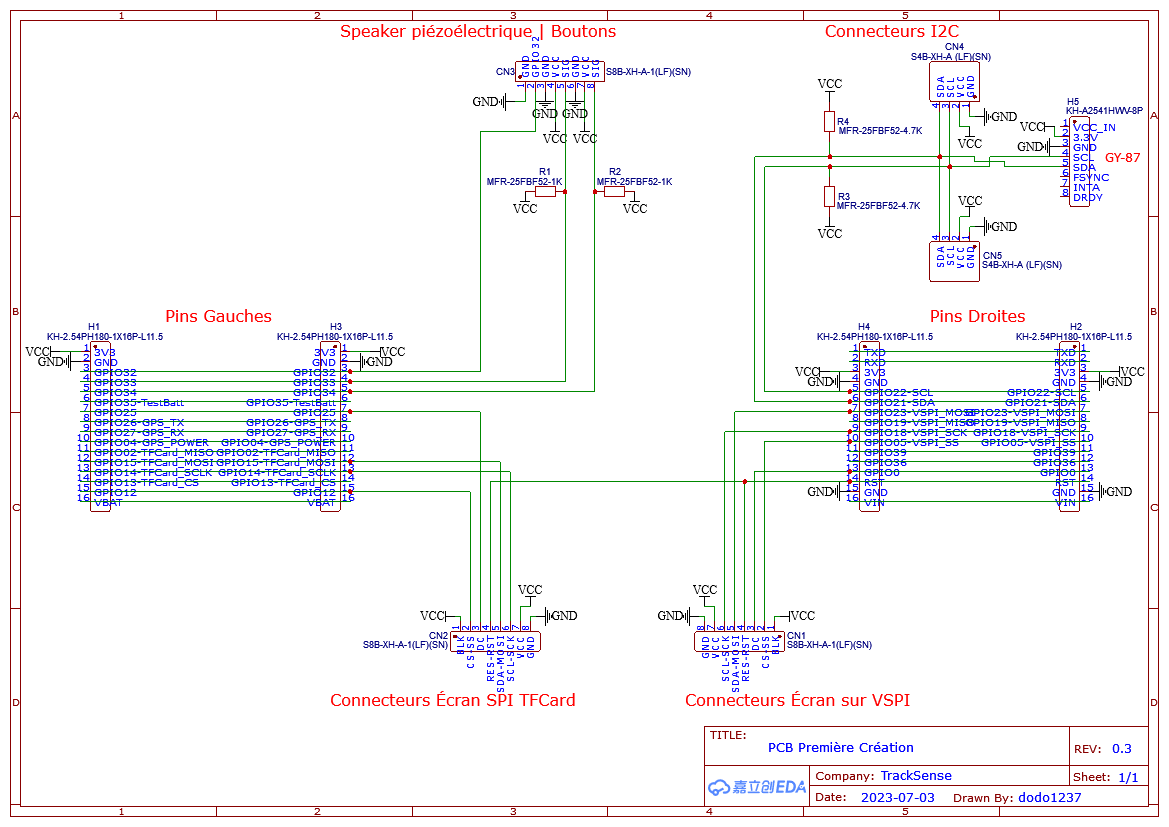
Composants/PCB/V1.0/Schematic_TrackSense_2023-07-17.png
