dodo-12-37/TrackSense/Composants/Écran/Connection Similar GC9A01 Modules.png

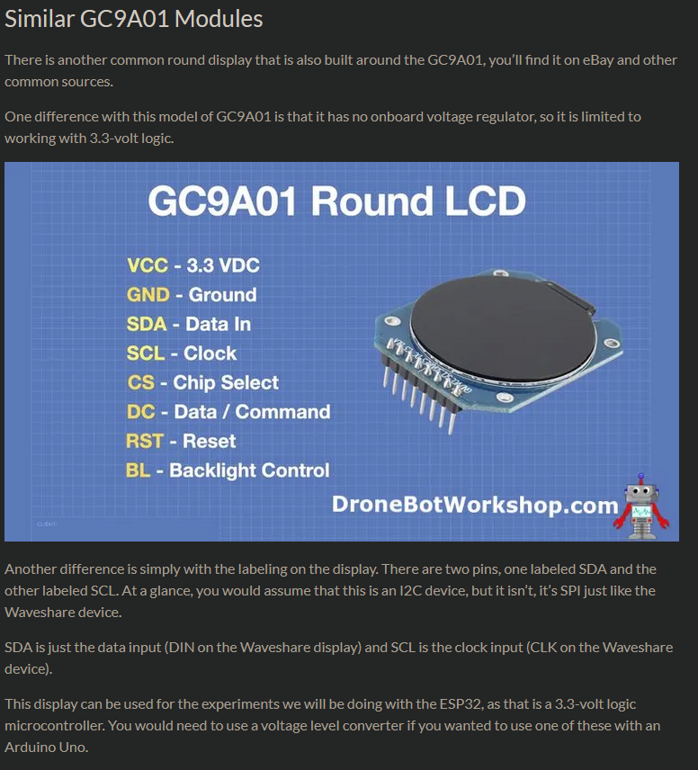
Composants/Écran/Connection Similar GC9A01 Modules.png
