dodo-12-37/TrackSense/Composants/Écran/Diagramme PINs.png

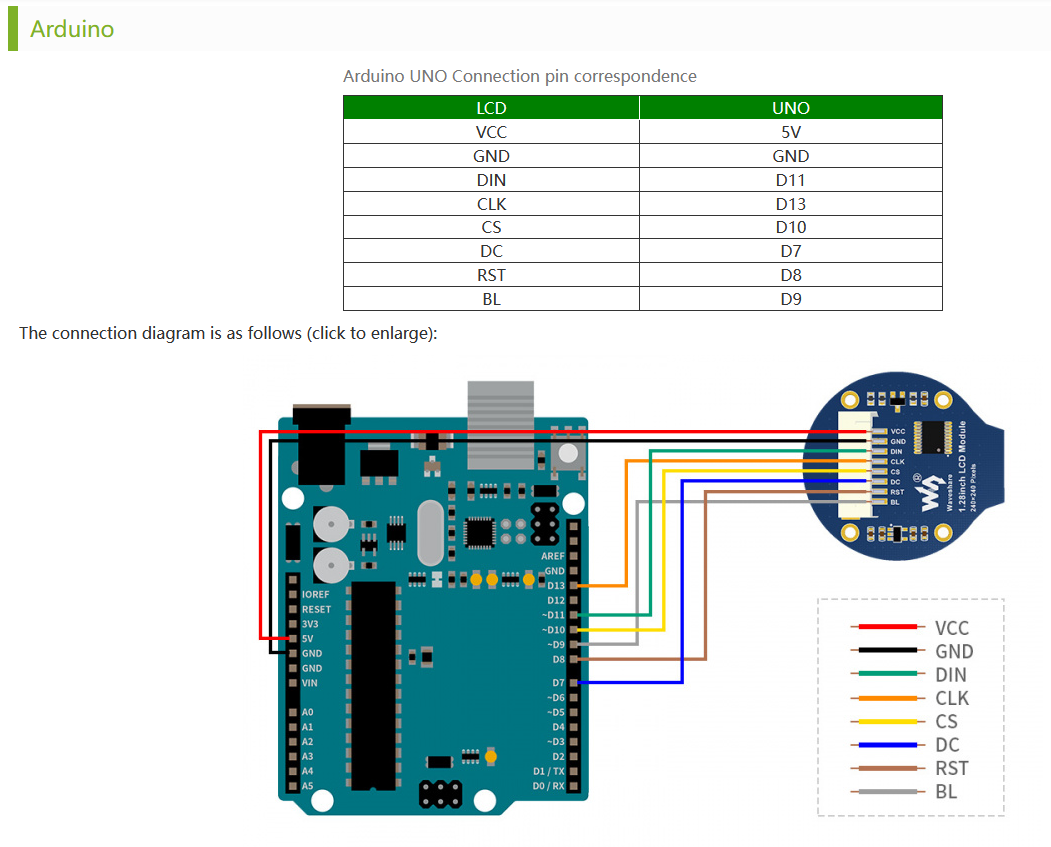
Composants/Écran/Diagramme PINs.png
