dodo-12-37/TrackSense/Composants/Écran/Dimension Sensor ER-TFTM1.28-1 with No Touch Panel Outline Drawing.png

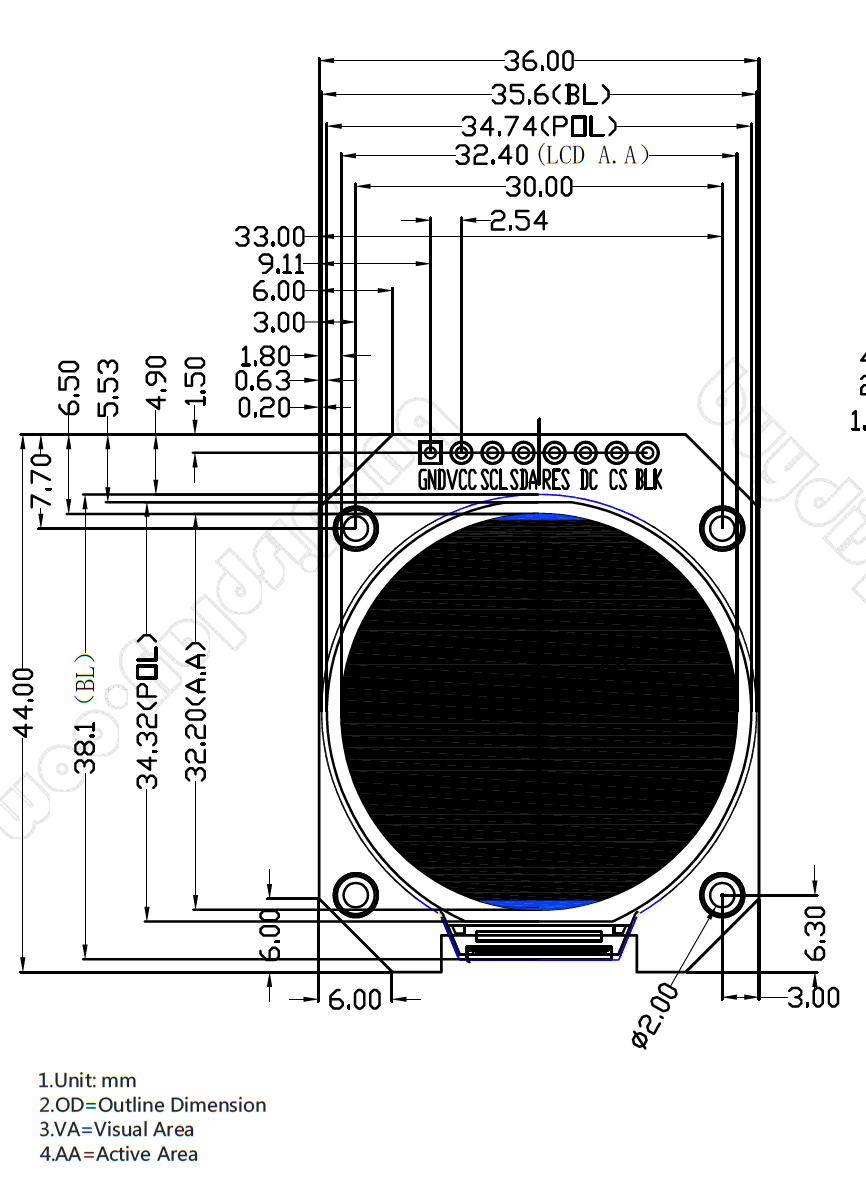
Composants/Écran/Dimension Sensor ER-TFTM1.28-1 with No Touch Panel Outline Drawing.png
