dodo-12-37/TrackSense/Composants/Écran/Explications des PINs.png

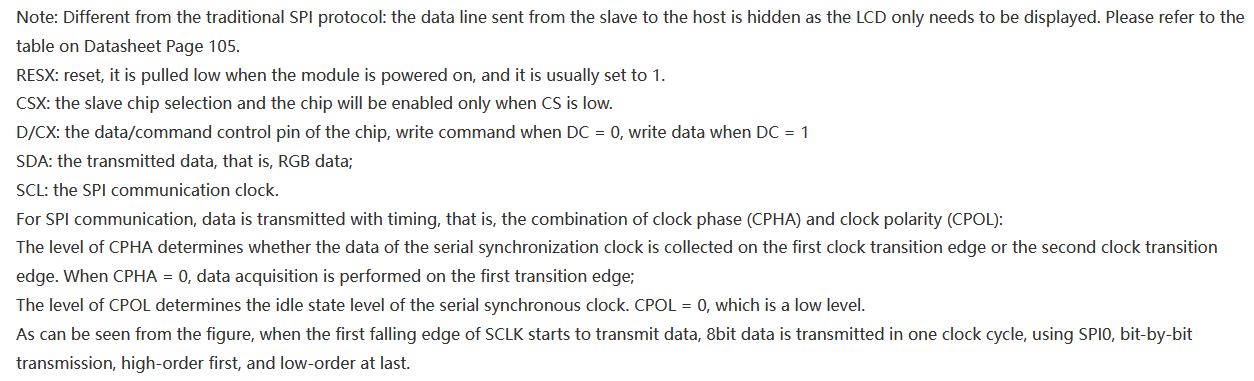
Composants/Écran/Explications des PINs.png
