dodo-12-37/TrackSense/Composants/Écran/IPS-LCD-1.28-240x240-Round-Display-GC9A01-Square-PCB.jpg

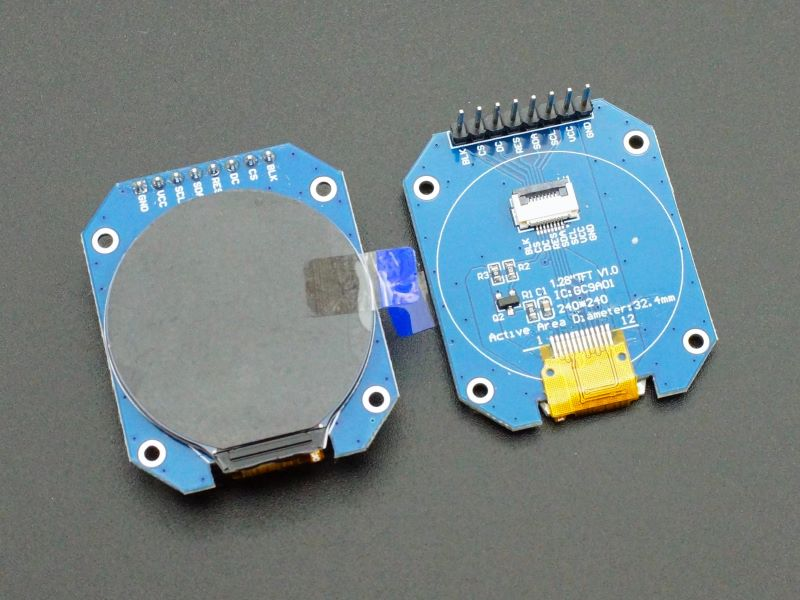
Composants/Écran/IPS-LCD-1.28-240x240-Round-Display-GC9A01-Square-PCB.jpg
