dodo-12-37/TrackSense/Composants/Écran/Module Connection.png

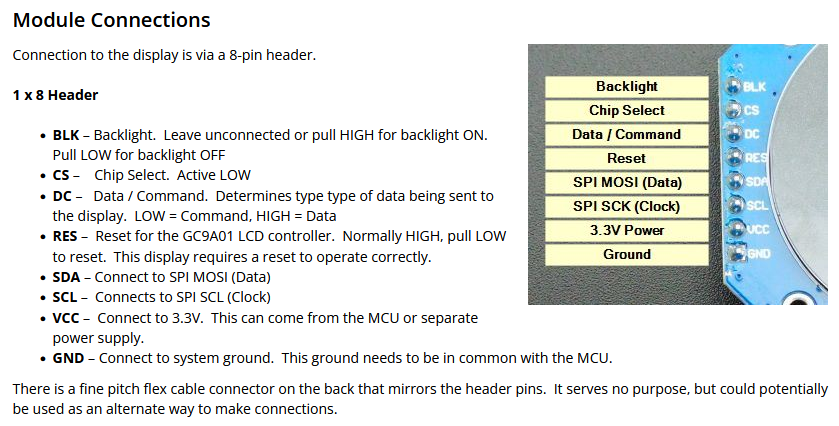
Composants/Écran/Module Connection.png
