dodo-12-37/TrackSense/Composants/Écran/TFT LCD Display Module GC9A01 - Description.jpg

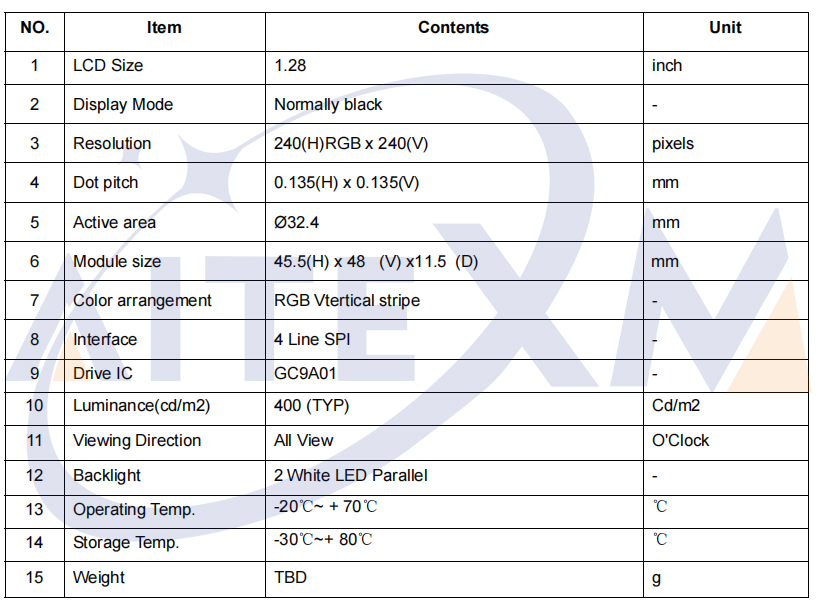
Composants/Écran/TFT LCD Display Module GC9A01 - Description.jpg
