dodo-12-37/TrackSense/Composants/Écran/TFT LCD Display Module GC9A01 - Mesure Physique.jpg

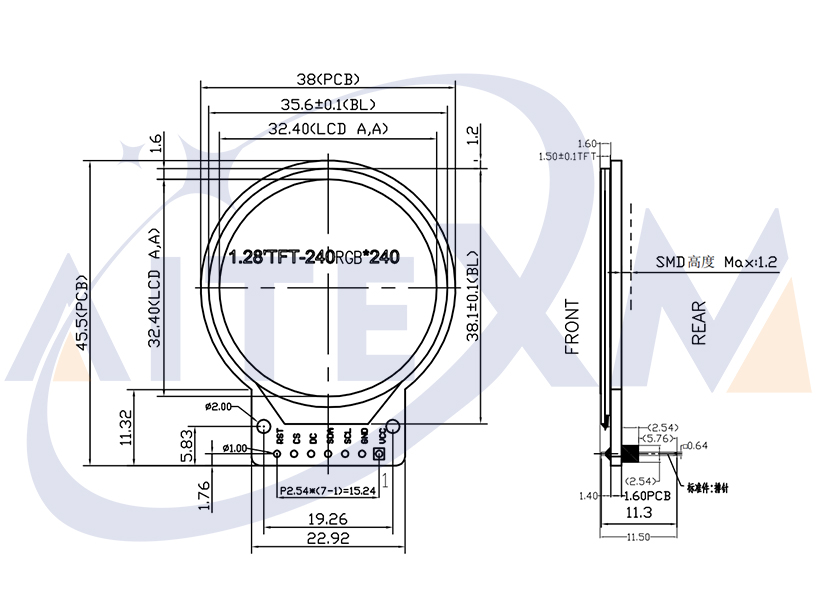
Composants/Écran/TFT LCD Display Module GC9A01 - Mesure Physique.jpg
