dodo-12-37/TrackSense/Composants/Écran/TFT LCD Display Module GC9A01 - Pins Definition.jpg

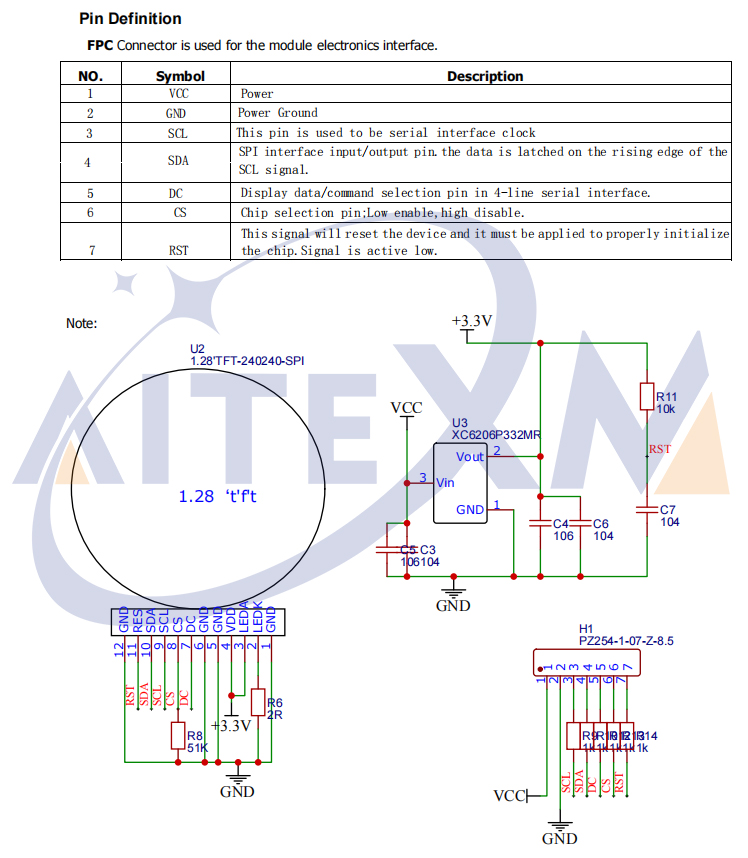
Composants/Écran/TFT LCD Display Module GC9A01 - Pins Definition.jpg
