dodo-12-37/TrackSense/Composants/Lilygo/Installation Panneau Solaire.jpg

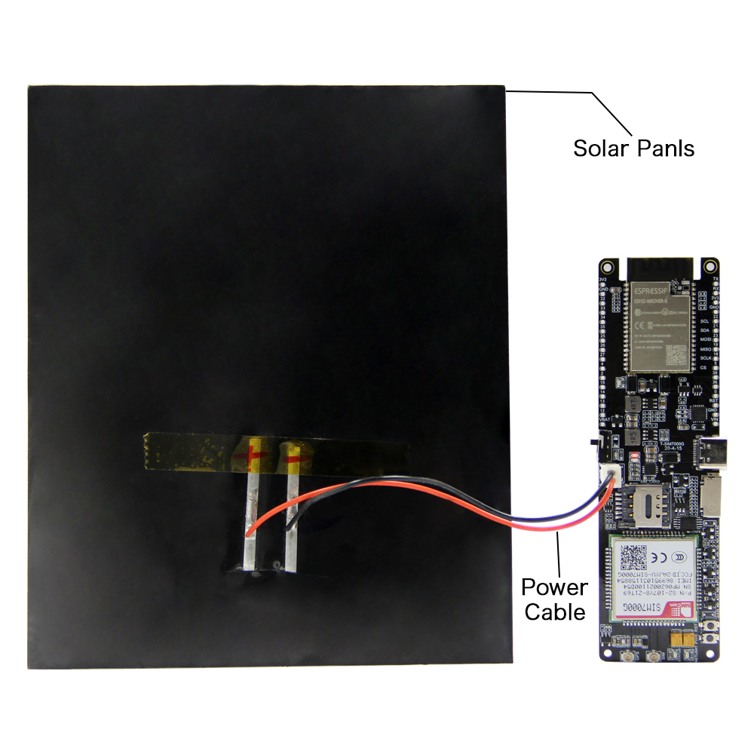
Composants/Lilygo/Installation Panneau Solaire.jpg
